yamamo2shun1/JUMBLEQ/STM32CubeIDE/JUMBLEQ/Appli/Core/Inc/led_control.h

/*
 * led_control.h
 *
 *  Created on: Nov 13, 2025
 *      Author: Shunichi Yamamoto
 */

#ifndef INC_LED_CONTROL_H_
#define INC_LED_CONTROL_H_

#include <stdint.h>

void led_update_color_state(void);
void led_reset_buffer(void);

void led_tx_blinking_task(void);
void led_rx_blinking_task(void);

void led_set_color(uint8_t index, uint8_t red, uint8_t green, uint8_t blue);
void led_renew_buffer(void);
void led_rgb_task(void);
void led_notify_save_success(void);

#endif /* INC_LED_CONTROL_H_ */
