yamamo2shun1/JUMBLEQ/STM32CubeIDE/JUMBLEQ/Appli/Core/Inc/JUMBLEQ_DSP_ADAU146xSchematic_1.h

/* 
 * File:	C:\Users\shun\JUMBLEQ\SigmaStudio+\exported_code\JUMBLEQ_DSP_ADAU146xSchematic_1.h
 * Created:	Tuesday, 15 September 2026 12:42 PM
 * Description:	ADAU146xSchematic_1 program data.
 * 
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
 * This software may only be used to program products purchased from 
 * Analog Devices for incorporation by you into audio products that 
 * are intended for resale to audio product end users.This software 
 * may not be distributed whole or in any part to third parties. 
 * 
 * Copyright © 2026 Analog Devices, Inc. All rights reserved.
 */

#include "SigmaStudioFW.h"

#ifndef __JUMBLEQ_DSP_ADAU146XSCHEMATIC_1_H__
#define __JUMBLEQ_DSP_ADAU146XSCHEMATIC_1_H__

/* DSP Ram Data */
#define DM1_DATA_SIZE_ADAU146XSCHEMATIC_1 912
#define DM1_DATA_ADDR_ADAU146XSCHEMATIC_1 24576
ADI_REG_TYPE DM1_DATA_ADAU146XSCHEMATIC_1_Data[DM1_DATA_SIZE_ADAU146XSCHEMATIC_1] = {
0x00, 0x00, 0x00, 0x00, 
0x00, 0x00, 0x00, 0x00, 
0x00, 0x00, 0x00, 0x00, 
0x00, 0x00, 0x00, 0x00, 
0x00, 0x00, 0x00, 0x00, 
0x00, 0x00, 0x00, 0x00, 
0x00, 0x00, 0x00, 0x00, 
0x00, 0x00, 0x00, 0x00, 
0x00, 0x00, 0x00, 0x00, 
0x00, 0x00, 0x20, 0x8A, 
0x00, 0x00, 0x00, 0x00, 
0x00, 0x00, 0x04, 0x10, 
0x00, 0x00, 0x00, 0x00, 
0x00, 0x00, 0x20, 0x8A, 
0x00, 0x00, 0x00, 0x00, 
0x00, 0x00, 0x04, 0x10, 
0x00, 0x00, 0x00, 0x00, 
0x00, 0x00, 0x20, 0x8A, 
0x00, 0x00, 0x00, 0x00, 
0x00, 0x00, 0x00, 0x00, 
0x00, 0x00, 0x00, 0x00, 
0x00, 0x00, 0x00, 0x00, 
0x00, 0x00, 0x00, 0x00, 
0x00, 0x00, 0x00, 0x00, 
0x00, 0x00, 0x00, 0x00, 
0x00, 0x00, 0x00, 0x00, 
0x00, 0x00, 0x00, 0x00, 
0x00, 0x00, 0x00, 0x00, 
0x00, 0x00, 0x00, 0x00, 
0x00, 0x00, 0x00, 0x00, 
0x00, 0x00, 0x00, 0x00, 
0x00, 0x00, 0x00, 0x00, 
0x00, 0x00, 0x00, 0x00, 
0x00, 0x00, 0x00, 0x00, 
0x00, 0x00, 0x00, 0x00, 
0x00, 0x00, 0x00, 0x00, 
0x00, 0x00, 0x00, 0x00, 
0x00, 0x00, 0x00, 0x00, 
0x00, 0x00, 0x00, 0x00, 
0x00, 0x00, 0x00, 0x00, 
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
};

/* DSP Program Data */
#define PROGRAM_DATA_SIZE_ADAU146XSCHEMATIC_1 2936
#define PROGRAM_DATA_ADDR_ADAU146XSCHEMATIC_1 49152
ADI_REG_TYPE PROGRAM_DATA_ADAU146XSCHEMATIC_1_Data[PROGRAM_DATA_SIZE_ADAU146XSCHEMATIC_1] = {
0x00, 0x00, 0x00, 0x02, 
0x0C, 0x00, 0xDC, 0xDC, 
0x0D, 0x00, 0xFF, 0xD2, 
0x0D, 0x00, 0xFF, 0xD0, 
0x0D, 0x00, 0xF4, 0x50, 
0x0D, 0x00, 0xF4, 0x00, 
0xC0, 0x00, 0x23, 0x80, 
0x80, 0x00, 0x00, 0x00, 
0xC0, 0x00, 0x23, 0x00, 
0x80, 0x00, 0x00, 0x00, 
0xC0, 0x00, 0x23, 0xC0, 
0x80, 0x00, 0x00, 0x10, 
0xC0, 0x00, 0x22, 0x00, 
0x80, 0x00, 0x00, 0x00, 
0x08, 0x80, 0xDC, 0xE0, 
0x0C, 0x00, 0xDC, 0xDC, 
0x0A, 0x21, 0x00, 0x12, 
0x08, 0x00, 0x00, 0x10, 
0x01, 0x00, 0x00, 0x14, 
0x06, 0x40, 0x40, 0x10, 
0x0A, 0x21, 0x00, 0x16, 
0x08, 0x00, 0x00, 0x14, 
0x01, 0x00, 0x00, 0x18, 
0x06, 0x40, 0x50, 0x10, 
0x0A, 0x21, 0x00, 0x1A, 
0x08, 0x00, 0x00, 0x18, 
0x01, 0x00, 0x00, 0x1C, 
0x06, 0x40, 0x50, 0x10, 
0xC0, 0x00, 0x20, 0x00, 
0x80, 0x00, 0x00, 0x2F, 
0x0D, 0x00, 0xFF, 0xC1, 
0xC0, 0x00, 0x20, 0x00, 
0x80, 0x00, 0x00, 0x01, 
0x0D, 0x00, 0xF4, 0x62, 
0xC0, 0x00, 0x20, 0x00, 
0x80, 0x00, 0x00, 0x00, 
0x0D, 0x00, 0xF4, 0x62, 
0xC0, 0x00, 0x20, 0x00, 
0x80, 0x00, 0x00, 0x02, 
0x0D, 0x00, 0xFF, 0xD1, 
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
};

/* DSP Parameter (Coefficient) Data */
#define DM0_DATA_SIZE_ADAU146XSCHEMATIC_1 696
#define DM0_DATA_ADDR_ADAU146XSCHEMATIC_1 0
ADI_REG_TYPE DM0_DATA_ADAU146XSCHEMATIC_1_Data[DM0_DATA_SIZE_ADAU146XSCHEMATIC_1] = {
0x00, 0x00, 0x00, 0x00, 
0x00, 0x00, 0x00, 0x00, 
0x00, 0x00, 0x00, 0x00, 
0x00, 0x00, 0x00, 0x00, 
0x00, 0x00, 0x00, 0x00, 
0x00, 0x00, 0x00, 0x00, 
0x00, 0x00, 0x00, 0x00, 
0x00, 0x00, 0x00, 0x00, 
0x00, 0x00, 0x00, 0x00, 
0x00, 0x00, 0x00, 0x00, 
0x00, 0x00, 0x00, 0x00, 
0x00, 0x00, 0x00, 0x00, 
0x00, 0x00, 0x00, 0x00, 
0x00, 0x00, 0x00, 0x00, 
0x00, 0x00, 0x00, 0x00, 
0x00, 0x00, 0x00, 0x00, 
0x00, 0x00, 0x00, 0x5C, 
0x00, 0x00, 0x00, 0x5C, 
0x00, 0x00, 0x00, 0x0C, 
0x00, 0x00, 0x00, 0x00, 
0x00, 0x00, 0x00, 0x14, 
0x00, 0x00, 0x00, 0x14, 
0x00, 0x00, 0x00, 0x90, 
0x00, 0x00, 0x00, 0x00, 
0x00, 0x00, 0x00, 0xA4, 
0x00, 0x00, 0x00, 0xA4, 
0x00, 0x00, 0x00, 0x3C, 
0x00, 0x00, 0x00, 0x00, 
0xFF, 0x00, 0x62, 0xF7, 
0x01, 0xFF, 0x3A, 0x12, 
0xFF, 0x00, 0x62, 0xF7, 
0xFF, 0x00, 0xC5, 0xD7, 
0x01, 0xFF, 0x39, 0xFC, 
0xFF, 0x00, 0x29, 0x0E, 
0x01, 0xFF, 0xAD, 0xE4, 
0xFF, 0x00, 0x29, 0x0E, 
0xFF, 0x00, 0x52, 0x05, 
0x01, 0xFF, 0xAD, 0xCE, 
0xFF, 0xEF, 0xD6, 0xFE, 
0x00, 0x00, 0x89, 0xC6, 
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
};

/* Register Default - SOFT_RESET */
#define R0_SOFT_RESET_SIZE_ADAU146XSCHEMATIC_1 2
#define R0_SOFT_RESET_ADDR_ADAU146XSCHEMATIC_1 63632
ADI_REG_TYPE R0_SOFT_RESET_ADAU146XSCHEMATIC_1_Data[R0_SOFT_RESET_SIZE_ADAU146XSCHEMATIC_1] = {
0x00, 0x00, 
};

/* Register Default - SOFT_RESET */
#define R1_SOFT_RESET_SIZE_ADAU146XSCHEMATIC_1 2
#define R1_SOFT_RESET_ADDR_ADAU146XSCHEMATIC_1 63632
ADI_REG_TYPE R1_SOFT_RESET_ADAU146XSCHEMATIC_1_Data[R1_SOFT_RESET_SIZE_ADAU146XSCHEMATIC_1] = {
0x00, 0x01, 
};

/* Register Default - Reset Delay */
#define R2_RESET_DELAY_SIZE_ADAU146XSCHEMATIC_1 2
#define R2_RESET_DELAY_ADDR_ADAU146XSCHEMATIC_1 0
ADI_REG_TYPE R2_RESET_DELAY_ADAU146XSCHEMATIC_1_Data[R2_RESET_DELAY_SIZE_ADAU146XSCHEMATIC_1] = {
0x00, 0xFF, 
};

/* Register Default - HIBERNATE */
#define R3_HIBERNATE_SIZE_ADAU146XSCHEMATIC_1 2
#define R3_HIBERNATE_ADDR_ADAU146XSCHEMATIC_1 62464
ADI_REG_TYPE R3_HIBERNATE_ADAU146XSCHEMATIC_1_Data[R3_HIBERNATE_SIZE_ADAU146XSCHEMATIC_1] = {
0x00, 0x00, 
};

/* Register Default - HIBERNATE */
#define R4_HIBERNATE_SIZE_ADAU146XSCHEMATIC_1 2
#define R4_HIBERNATE_ADDR_ADAU146XSCHEMATIC_1 62464
ADI_REG_TYPE R4_HIBERNATE_ADAU146XSCHEMATIC_1_Data[R4_HIBERNATE_SIZE_ADAU146XSCHEMATIC_1] = {
0x00, 0x01, 
};

/* Register Default - Hibernate Delay */
#define R5_HIBERNATE_DELAY_SIZE_ADAU146XSCHEMATIC_1 2
#define R5_HIBERNATE_DELAY_ADDR_ADAU146XSCHEMATIC_1 0
ADI_REG_TYPE R5_HIBERNATE_DELAY_ADAU146XSCHEMATIC_1_Data[R5_HIBERNATE_DELAY_SIZE_ADAU146XSCHEMATIC_1] = {
0x00, 0xFF, 
};

/* Register Default - KILL_CORE */
#define R6_KILL_CORE_SIZE_ADAU146XSCHEMATIC_1 2
#define R6_KILL_CORE_ADDR_ADAU146XSCHEMATIC_1 62467
ADI_REG_TYPE R6_KILL_CORE_ADAU146XSCHEMATIC_1_Data[R6_KILL_CORE_SIZE_ADAU146XSCHEMATIC_1] = {
0x00, 0x00, 
};

/* Register Default - KILL_CORE */
#define R7_KILL_CORE_SIZE_ADAU146XSCHEMATIC_1 2
#define R7_KILL_CORE_ADDR_ADAU146XSCHEMATIC_1 62467
ADI_REG_TYPE R7_KILL_CORE_ADAU146XSCHEMATIC_1_Data[R7_KILL_CORE_SIZE_ADAU146XSCHEMATIC_1] = {
0x00, 0x01, 
};

/* Register Default - PLL_ENABLE */
#define R8_PLL_ENABLE_SIZE_ADAU146XSCHEMATIC_1 2
#define R8_PLL_ENABLE_ADDR_ADAU146XSCHEMATIC_1 61443
ADI_REG_TYPE R8_PLL_ENABLE_ADAU146XSCHEMATIC_1_Data[R8_PLL_ENABLE_SIZE_ADAU146XSCHEMATIC_1] = {
0x00, 0x00, 
};

/* Register Default - PLL_CTRL1 Register */
#define R9_PLL_CTRL1_REGISTER_SIZE_ADAU146XSCHEMATIC_1 2
#define R9_PLL_CTRL1_REGISTER_ADDR_ADAU146XSCHEMATIC_1 61441
ADI_REG_TYPE R9_PLL_CTRL1_REGISTER_ADAU146XSCHEMATIC_1_Data[R9_PLL_CTRL1_REGISTER_SIZE_ADAU146XSCHEMATIC_1] = {
0x00, 0x02, 
};

/* Register Default - PLL_CLK_SRC Register */
#define R10_PLL_CLK_SRC_REGISTER_SIZE_ADAU146XSCHEMATIC_1 2
#define R10_PLL_CLK_SRC_REGISTER_ADDR_ADAU146XSCHEMATIC_1 61442
ADI_REG_TYPE R10_PLL_CLK_SRC_REGISTER_ADAU146XSCHEMATIC_1_Data[R10_PLL_CLK_SRC_REGISTER_SIZE_ADAU146XSCHEMATIC_1] = {
0x00, 0x01, 
};

/* Register Default - MCLK_OUT Register */
#define R11_MCLK_OUT_REGISTER_SIZE_ADAU146XSCHEMATIC_1 2
#define R11_MCLK_OUT_REGISTER_ADDR_ADAU146XSCHEMATIC_1 61445
ADI_REG_TYPE R11_MCLK_OUT_REGISTER_ADAU146XSCHEMATIC_1_Data[R11_MCLK_OUT_REGISTER_SIZE_ADAU146XSCHEMATIC_1] = {
0x00, 0x07, 
};

/* Register Default - PLL_ENABLE Register */
#define R12_PLL_ENABLE_REGISTER_SIZE_ADAU146XSCHEMATIC_1 2
#define R12_PLL_ENABLE_REGISTER_ADDR_ADAU146XSCHEMATIC_1 61443
ADI_REG_TYPE R12_PLL_ENABLE_REGISTER_ADAU146XSCHEMATIC_1_Data[R12_PLL_ENABLE_REGISTER_SIZE_ADAU146XSCHEMATIC_1] = {
0x00, 0x01, 
};

/* Register Default - PLL Lock Delay */
#define R13_PLL_LOCK_DELAY_SIZE_ADAU146XSCHEMATIC_1 2
#define R13_PLL_LOCK_DELAY_ADDR_ADAU146XSCHEMATIC_1 0
ADI_REG_TYPE R13_PLL_LOCK_DELAY_ADAU146XSCHEMATIC_1_Data[R13_PLL_LOCK_DELAY_SIZE_ADAU146XSCHEMATIC_1] = {
0x00, 0xFF, 
};

/* Register Default - POWER_ENABLE0 Register */
#define R14_POWER_ENABLE0_REGISTER_SIZE_ADAU146XSCHEMATIC_1 2
#define R14_POWER_ENABLE0_REGISTER_ADDR_ADAU146XSCHEMATIC_1 61520
ADI_REG_TYPE R14_POWER_ENABLE0_REGISTER_ADAU146XSCHEMATIC_1_Data[R14_POWER_ENABLE0_REGISTER_SIZE_ADAU146XSCHEMATIC_1] = {
0x1F, 0xFF, 
};

/* Register Default - POWER_ENABLE1 Register */
#define R15_POWER_ENABLE1_REGISTER_SIZE_ADAU146XSCHEMATIC_1 2
#define R15_POWER_ENABLE1_REGISTER_ADDR_ADAU146XSCHEMATIC_1 61521
ADI_REG_TYPE R15_POWER_ENABLE1_REGISTER_ADAU146XSCHEMATIC_1_Data[R15_POWER_ENABLE1_REGISTER_SIZE_ADAU146XSCHEMATIC_1] = {
0x00, 0x1F, 
};

/* Register Default - CLK_GEN1_M */
#define R16_CLK_GEN1_M_SIZE_ADAU146XSCHEMATIC_1 2
#define R16_CLK_GEN1_M_ADDR_ADAU146XSCHEMATIC_1 61472
ADI_REG_TYPE R16_CLK_GEN1_M_ADAU146XSCHEMATIC_1_Data[R16_CLK_GEN1_M_SIZE_ADAU146XSCHEMATIC_1] = {
0x00, 0x03, 
};

/* Register Default - CLK_GEN2_M */
#define R17_CLK_GEN2_M_SIZE_ADAU146XSCHEMATIC_1 2
#define R17_CLK_GEN2_M_ADDR_ADAU146XSCHEMATIC_1 61474
ADI_REG_TYPE R17_CLK_GEN2_M_ADAU146XSCHEMATIC_1_Data[R17_CLK_GEN2_M_SIZE_ADAU146XSCHEMATIC_1] = {
0x00, 0x06, 
};

/* Register Default - ASRC_INPUT0 */
#define R18_ASRC_INPUT0_SIZE_ADAU146XSCHEMATIC_1 2
#define R18_ASRC_INPUT0_ADDR_ADAU146XSCHEMATIC_1 61696
ADI_REG_TYPE R18_ASRC_INPUT0_ADAU146XSCHEMATIC_1_Data[R18_ASRC_INPUT0_SIZE_ADAU146XSCHEMATIC_1] = {
0x00, 0x01, 
};

/* Register Default - ASRC_INPUT1 */
#define R19_ASRC_INPUT1_SIZE_ADAU146XSCHEMATIC_1 2
#define R19_ASRC_INPUT1_ADDR_ADAU146XSCHEMATIC_1 61697
ADI_REG_TYPE R19_ASRC_INPUT1_ADAU146XSCHEMATIC_1_Data[R19_ASRC_INPUT1_SIZE_ADAU146XSCHEMATIC_1] = {
0x00, 0x09, 
};

/* Register Default - ASRC_INPUT2 */
#define R20_ASRC_INPUT2_SIZE_ADAU146XSCHEMATIC_1 2
#define R20_ASRC_INPUT2_ADDR_ADAU146XSCHEMATIC_1 61698
ADI_REG_TYPE R20_ASRC_INPUT2_ADAU146XSCHEMATIC_1_Data[R20_ASRC_INPUT2_SIZE_ADAU146XSCHEMATIC_1] = {
0x00, 0x02, 
};

/* Register Default - ASRC_INPUT3 */
#define R21_ASRC_INPUT3_SIZE_ADAU146XSCHEMATIC_1 2
#define R21_ASRC_INPUT3_ADDR_ADAU146XSCHEMATIC_1 61699
ADI_REG_TYPE R21_ASRC_INPUT3_ADAU146XSCHEMATIC_1_Data[R21_ASRC_INPUT3_SIZE_ADAU146XSCHEMATIC_1] = {
0x00, 0x02, 
};

/* Register Default - ASRC_OUT_RATE0 */
#define R22_ASRC_OUT_RATE0_SIZE_ADAU146XSCHEMATIC_1 2
#define R22_ASRC_OUT_RATE0_ADDR_ADAU146XSCHEMATIC_1 61760
ADI_REG_TYPE R22_ASRC_OUT_RATE0_ADAU146XSCHEMATIC_1_Data[R22_ASRC_OUT_RATE0_SIZE_ADAU146XSCHEMATIC_1] = {
0x00, 0x05, 
};

/* Register Default - ASRC_OUT_RATE1 */
#define R23_ASRC_OUT_RATE1_SIZE_ADAU146XSCHEMATIC_1 2
#define R23_ASRC_OUT_RATE1_ADDR_ADAU146XSCHEMATIC_1 61761
ADI_REG_TYPE R23_ASRC_OUT_RATE1_ADAU146XSCHEMATIC_1_Data[R23_ASRC_OUT_RATE1_SIZE_ADAU146XSCHEMATIC_1] = {
0x00, 0x05, 
};

/* Register Default - ASRC_OUT_RATE2 */
#define R24_ASRC_OUT_RATE2_SIZE_ADAU146XSCHEMATIC_1 2
#define R24_ASRC_OUT_RATE2_ADDR_ADAU146XSCHEMATIC_1 61762
ADI_REG_TYPE R24_ASRC_OUT_RATE2_ADAU146XSCHEMATIC_1_Data[R24_ASRC_OUT_RATE2_SIZE_ADAU146XSCHEMATIC_1] = {
0x00, 0x01, 
};

/* Register Default - ASRC_OUT_RATE3 */
#define R25_ASRC_OUT_RATE3_SIZE_ADAU146XSCHEMATIC_1 2
#define R25_ASRC_OUT_RATE3_ADDR_ADAU146XSCHEMATIC_1 61763
ADI_REG_TYPE R25_ASRC_OUT_RATE3_ADAU146XSCHEMATIC_1_Data[R25_ASRC_OUT_RATE3_SIZE_ADAU146XSCHEMATIC_1] = {
0x00, 0x01, 
};

/* Register Default - SOUT_SOURCE0 */
#define R26_SOUT_SOURCE0_SIZE_ADAU146XSCHEMATIC_1 2
#define R26_SOUT_SOURCE0_ADDR_ADAU146XSCHEMATIC_1 61824
ADI_REG_TYPE R26_SOUT_SOURCE0_ADAU146XSCHEMATIC_1_Data[R26_SOUT_SOURCE0_SIZE_ADAU146XSCHEMATIC_1] = {
0x00, 0x13, 
};

/* Register Default - SOUT_SOURCE1 */
#define R27_SOUT_SOURCE1_SIZE_ADAU146XSCHEMATIC_1 2
#define R27_SOUT_SOURCE1_ADDR_ADAU146XSCHEMATIC_1 61825
ADI_REG_TYPE R27_SOUT_SOURCE1_ADAU146XSCHEMATIC_1_Data[R27_SOUT_SOURCE1_SIZE_ADAU146XSCHEMATIC_1] = {
0x00, 0x1B, 
};

/* Register Default - SOUT_SOURCE2 */
#define R28_SOUT_SOURCE2_SIZE_ADAU146XSCHEMATIC_1 2
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
0x90, 0x41, 
};

/* Register Default - SERIAL_BYTE_3_0 */
#define R54_SERIAL_BYTE_3_0_SIZE_ADAU146XSCHEMATIC_1 2
#define R54_SERIAL_BYTE_3_0_ADDR_ADAU146XSCHEMATIC_1 61964
ADI_REG_TYPE R54_SERIAL_BYTE_3_0_ADAU146XSCHEMATIC_1_Data[R54_SERIAL_BYTE_3_0_SIZE_ADAU146XSCHEMATIC_1] = {
0x90, 0x00, 
};

/* Register Default - SERIAL_BYTE_4_0 */
#define R55_SERIAL_BYTE_4_0_SIZE_ADAU146XSCHEMATIC_1 2
#define R55_SERIAL_BYTE_4_0_ADDR_ADAU146XSCHEMATIC_1 61968
ADI_REG_TYPE R55_SERIAL_BYTE_4_0_ADAU146XSCHEMATIC_1_Data[R55_SERIAL_BYTE_4_0_SIZE_ADAU146XSCHEMATIC_1] = {
0x90, 0x49, 
};

/* Register Default - SERIAL_BYTE_4_1 */
#define R56_SERIAL_BYTE_4_1_SIZE_ADAU146XSCHEMATIC_1 2
#define R56_SERIAL_BYTE_4_1_ADDR_ADAU146XSCHEMATIC_1 61969
ADI_REG_TYPE R56_SERIAL_BYTE_4_1_ADAU146XSCHEMATIC_1_Data[R56_SERIAL_BYTE_4_1_SIZE_ADAU146XSCHEMATIC_1] = {
0x00, 0x0A, 
};

/* Register Default - SERIAL_BYTE_5_0 */
#define R57_SERIAL_BYTE_5_0_SIZE_ADAU146XSCHEMATIC_1 2
#define R57_SERIAL_BYTE_5_0_ADDR_ADAU146XSCHEMATIC_1 61972
ADI_REG_TYPE R57_SERIAL_BYTE_5_0_ADAU146XSCHEMATIC_1_Data[R57_SERIAL_BYTE_5_0_SIZE_ADAU146XSCHEMATIC_1] = {
0x90, 0x41, 
};

/* Register Default - SERIAL_BYTE_6_0 */
#define R58_SERIAL_BYTE_6_0_SIZE_ADAU146XSCHEMATIC_1 2
#define R58_SERIAL_BYTE_6_0_ADDR_ADAU146XSCHEMATIC_1 61976
ADI_REG_TYPE R58_SERIAL_BYTE_6_0_ADAU146XSCHEMATIC_1_Data[R58_SERIAL_BYTE_6_0_SIZE_ADAU146XSCHEMATIC_1] = {
0x90, 0x40, 
};

/* Register Default - SERIAL_BYTE_7_0 */
#define R59_SERIAL_BYTE_7_0_SIZE_ADAU146XSCHEMATIC_1 2
#define R59_SERIAL_BYTE_7_0_ADDR_ADAU146XSCHEMATIC_1 61980
ADI_REG_TYPE R59_SERIAL_BYTE_7_0_ADAU146XSCHEMATIC_1_Data[R59_SERIAL_BYTE_7_0_SIZE_ADAU146XSCHEMATIC_1] = {
0x90, 0x00, 
};

/* Register Default - KILL_CORE */
#define R63_KILL_CORE_SIZE_ADAU146XSCHEMATIC_1 2
#define R63_KILL_CORE_ADDR_ADAU146XSCHEMATIC_1 62467
ADI_REG_TYPE R63_KILL_CORE_ADAU146XSCHEMATIC_1_Data[R63_KILL_CORE_SIZE_ADAU146XSCHEMATIC_1] = {
0x00, 0x00, 
};

/* Register Default - START_ADDRESS */
#define R64_START_ADDRESS_SIZE_ADAU146XSCHEMATIC_1 2
#define R64_START_ADDRESS_ADDR_ADAU146XSCHEMATIC_1 62468
ADI_REG_TYPE R64_START_ADDRESS_ADAU146XSCHEMATIC_1_Data[R64_START_ADDRESS_SIZE_ADAU146XSCHEMATIC_1] = {
0x00, 0x00, 
};

/* Register Default - START_PULSE */
#define R65_START_PULSE_SIZE_ADAU146XSCHEMATIC_1 2
#define R65_START_PULSE_ADDR_ADAU146XSCHEMATIC_1 62465
ADI_REG_TYPE R65_START_PULSE_ADAU146XSCHEMATIC_1_Data[R65_START_PULSE_SIZE_ADAU146XSCHEMATIC_1] = {
0x00, 0x02, 
};

/* Register Default - START_CORE */
#define R66_START_CORE_SIZE_ADAU146XSCHEMATIC_1 2
#define R66_START_CORE_ADDR_ADAU146XSCHEMATIC_1 62466
ADI_REG_TYPE R66_START_CORE_ADAU146XSCHEMATIC_1_Data[R66_START_CORE_SIZE_ADAU146XSCHEMATIC_1] = {
0x00, 0x00, 
};

/* Register Default - START_CORE */
#define R67_START_CORE_SIZE_ADAU146XSCHEMATIC_1 2
#define R67_START_CORE_ADDR_ADAU146XSCHEMATIC_1 62466
ADI_REG_TYPE R67_START_CORE_ADAU146XSCHEMATIC_1_Data[R67_START_CORE_SIZE_ADAU146XSCHEMATIC_1] = {
0x00, 0x01, 
};

/* Register Default - Start Delay */
#define R68_START_DELAY_SIZE_ADAU146XSCHEMATIC_1 2
#define R68_START_DELAY_ADDR_ADAU146XSCHEMATIC_1 0
ADI_REG_TYPE R68_START_DELAY_ADAU146XSCHEMATIC_1_Data[R68_START_DELAY_SIZE_ADAU146XSCHEMATIC_1] = {
0x00, 0x01, 
};

/* Register Default - HIBERNATE */
#define R69_HIBERNATE_SIZE_ADAU146XSCHEMATIC_1 2
#define R69_HIBERNATE_ADDR_ADAU146XSCHEMATIC_1 62464
ADI_REG_TYPE R69_HIBERNATE_ADAU146XSCHEMATIC_1_Data[R69_HIBERNATE_SIZE_ADAU146XSCHEMATIC_1] = {
0x00, 0x00, 
};

/* Default Download */
#define DEFAULT_DOWNLOAD_SIZE_ADAU146XSCHEMATIC_1 70

void default_download_ADAU146XSCHEMATIC_1()
{
	SIGMA_WRITE_REGISTER_BLOCK(DEVICE_ADDR_ADAU146XSCHEMATIC_1, R0_SOFT_RESET_ADDR_ADAU146XSCHEMATIC_1 , R0_SOFT_RESET_SIZE_ADAU146XSCHEMATIC_1 , R0_SOFT_RESET_ADAU146XSCHEMATIC_1_Data);
	SIGMA_WRITE_REGISTER_BLOCK(DEVICE_ADDR_ADAU146XSCHEMATIC_1, R1_SOFT_RESET_ADDR_ADAU146XSCHEMATIC_1 , R1_SOFT_RESET_SIZE_ADAU146XSCHEMATIC_1 , R1_SOFT_RESET_ADAU146XSCHEMATIC_1_Data);
	SIGMA_WRITE_DELAY(DEVICE_ADDR_ADAU146XSCHEMATIC_1, R2_RESET_DELAY_ADDR_ADAU146XSCHEMATIC_1 , R2_RESET_DELAY_SIZE_ADAU146XSCHEMATIC_1 , R2_RESET_DELAY_ADAU146XSCHEMATIC_1_Data);
	SIGMA_WRITE_REGISTER_BLOCK(DEVICE_ADDR_ADAU146XSCHEMATIC_1, R3_HIBERNATE_ADDR_ADAU146XSCHEMATIC_1 , R3_HIBERNATE_SIZE_ADAU146XSCHEMATIC_1 , R3_HIBERNATE_ADAU146XSCHEMATIC_1_Data);
	SIGMA_WRITE_REGISTER_BLOCK(DEVICE_ADDR_ADAU146XSCHEMATIC_1, R4_HIBERNATE_ADDR_ADAU146XSCHEMATIC_1 , R4_HIBERNATE_SIZE_ADAU146XSCHEMATIC_1 , R4_HIBERNATE_ADAU146XSCHEMATIC_1_Data);
	SIGMA_WRITE_DELAY(DEVICE_ADDR_ADAU146XSCHEMATIC_1, R5_HIBERNATE_DELAY_ADDR_ADAU146XSCHEMATIC_1 , R5_HIBERNATE_DELAY_SIZE_ADAU146XSCHEMATIC_1 , R5_HIBERNATE_DELAY_ADAU146XSCHEMATIC_1_Data);
	SIGMA_WRITE_REGISTER_BLOCK(DEVICE_ADDR_ADAU146XSCHEMATIC_1, R6_KILL_CORE_ADDR_ADAU146XSCHEMATIC_1 , R6_KILL_CORE_SIZE_ADAU146XSCHEMATIC_1 , R6_KILL_CORE_ADAU146XSCHEMATIC_1_Data);
	SIGMA_WRITE_REGISTER_BLOCK(DEVICE_ADDR_ADAU146XSCHEMATIC_1, R7_KILL_CORE_ADDR_ADAU146XSCHEMATIC_1 , R7_KILL_CORE_SIZE_ADAU146XSCHEMATIC_1 , R7_KILL_CORE_ADAU146XSCHEMATIC_1_Data);
	SIGMA_WRITE_REGISTER_BLOCK(DEVICE_ADDR_ADAU146XSCHEMATIC_1, R8_PLL_ENABLE_ADDR_ADAU146XSCHEMATIC_1 , R8_PLL_ENABLE_SIZE_ADAU146XSCHEMATIC_1 , R8_PLL_ENABLE_ADAU146XSCHEMATIC_1_Data);
	SIGMA_WRITE_REGISTER_BLOCK(DEVICE_ADDR_ADAU146XSCHEMATIC_1, R9_PLL_CTRL1_REGISTER_ADDR_ADAU146XSCHEMATIC_1 , R9_PLL_CTRL1_REGISTER_SIZE_ADAU146XSCHEMATIC_1 , R9_PLL_CTRL1_REGISTER_ADAU146XSCHEMATIC_1_Data);
	SIGMA_WRITE_REGISTER_BLOCK(DEVICE_ADDR_ADAU146XSCHEMATIC_1, R10_PLL_CLK_SRC_REGISTER_ADDR_ADAU146XSCHEMATIC_1 , R10_PLL_CLK_SRC_REGISTER_SIZE_ADAU146XSCHEMATIC_1 , R10_PLL_CLK_SRC_REGISTER_ADAU146XSCHEMATIC_1_Data);
	SIGMA_WRITE_REGISTER_BLOCK(DEVICE_ADDR_ADAU146XSCHEMATIC_1, R11_MCLK_OUT_REGISTER_ADDR_ADAU146XSCHEMATIC_1 , R11_MCLK_OUT_REGISTER_SIZE_ADAU146XSCHEMATIC_1 , R11_MCLK_OUT_REGISTER_ADAU146XSCHEMATIC_1_Data);
	SIGMA_WRITE_REGISTER_BLOCK(DEVICE_ADDR_ADAU146XSCHEMATIC_1, R12_PLL_ENABLE_REGISTER_ADDR_ADAU146XSCHEMATIC_1 , R12_PLL_ENABLE_REGISTER_SIZE_ADAU146XSCHEMATIC_1 , R12_PLL_ENABLE_REGISTER_ADAU146XSCHEMATIC_1_Data);
	SIGMA_WRITE_DELAY(DEVICE_ADDR_ADAU146XSCHEMATIC_1, R13_PLL_LOCK_DELAY_ADDR_ADAU146XSCHEMATIC_1 , R13_PLL_LOCK_DELAY_SIZE_ADAU146XSCHEMATIC_1 , R13_PLL_LOCK_DELAY_ADAU146XSCHEMATIC_1_Data);
	SIGMA_WRITE_REGISTER_BLOCK(DEVICE_ADDR_ADAU146XSCHEMATIC_1, R14_POWER_ENABLE0_REGISTER_ADDR_ADAU146XSCHEMATIC_1 , R14_POWER_ENABLE0_REGISTER_SIZE_ADAU146XSCHEMATIC_1 , R14_POWER_ENABLE0_REGISTER_ADAU146XSCHEMATIC_1_Data);
	SIGMA_WRITE_REGISTER_BLOCK(DEVICE_ADDR_ADAU146XSCHEMATIC_1, R15_POWER_ENABLE1_REGISTER_ADDR_ADAU146XSCHEMATIC_1 , R15_POWER_ENABLE1_REGISTER_SIZE_ADAU146XSCHEMATIC_1 , R15_POWER_ENABLE1_REGISTER_ADAU146XSCHEMATIC_1_Data);
	SIGMA_WRITE_REGISTER_BLOCK(DEVICE_ADDR_ADAU146XSCHEMATIC_1, R16_CLK_GEN1_M_ADDR_ADAU146XSCHEMATIC_1 , R16_CLK_GEN1_M_SIZE_ADAU146XSCHEMATIC_1 , R16_CLK_GEN1_M_ADAU146XSCHEMATIC_1_Data);
	SIGMA_WRITE_REGISTER_BLOCK(DEVICE_ADDR_ADAU146XSCHEMATIC_1, R17_CLK_GEN2_M_ADDR_ADAU146XSCHEMATIC_1 , R17_CLK_GEN2_M_SIZE_ADAU146XSCHEMATIC_1 , R17_CLK_GEN2_M_ADAU146XSCHEMATIC_1_Data);
	SIGMA_WRITE_REGISTER_BLOCK(DEVICE_ADDR_ADAU146XSCHEMATIC_1, R18_ASRC_INPUT0_ADDR_ADAU146XSCHEMATIC_1 , R18_ASRC_INPUT0_SIZE_ADAU146XSCHEMATIC_1 , R18_ASRC_INPUT0_ADAU146XSCHEMATIC_1_Data);
	SIGMA_WRITE_REGISTER_BLOCK(DEVICE_ADDR_ADAU146XSCHEMATIC_1, R19_ASRC_INPUT1_ADDR_ADAU146XSCHEMATIC_1 , R19_ASRC_INPUT1_SIZE_ADAU146XSCHEMATIC_1 , R19_ASRC_INPUT1_ADAU146XSCHEMATIC_1_Data);
	SIGMA_WRITE_REGISTER_BLOCK(DEVICE_ADDR_ADAU146XSCHEMATIC_1, R20_ASRC_INPUT2_ADDR_ADAU146XSCHEMATIC_1 , R20_ASRC_INPUT2_SIZE_ADAU146XSCHEMATIC_1 , R20_ASRC_INPUT2_ADAU146XSCHEMATIC_1_Data);
	SIGMA_WRITE_REGISTER_BLOCK(DEVICE_ADDR_ADAU146XSCHEMATIC_1, R21_ASRC_INPUT3_ADDR_ADAU146XSCHEMATIC_1 , R21_ASRC_INPUT3_SIZE_ADAU146XSCHEMATIC_1 , R21_ASRC_INPUT3_ADAU146XSCHEMATIC_1_Data);
	SIGMA_WRITE_REGISTER_BLOCK(DEVICE_ADDR_ADAU146XSCHEMATIC_1, R22_ASRC_OUT_RATE0_ADDR_ADAU146XSCHEMATIC_1 , R22_ASRC_OUT_RATE0_SIZE_ADAU146XSCHEMATIC_1 , R22_ASRC_OUT_RATE0_ADAU146XSCHEMATIC_1_Data);
	SIGMA_WRITE_REGISTER_BLOCK(DEVICE_ADDR_ADAU146XSCHEMATIC_1, R23_ASRC_OUT_RATE1_ADDR_ADAU146XSCHEMATIC_1 , R23_ASRC_OUT_RATE1_SIZE_ADAU146XSCHEMATIC_1 , R23_ASRC_OUT_RATE1_ADAU146XSCHEMATIC_1_Data);
	SIGMA_WRITE_REGISTER_BLOCK(DEVICE_ADDR_ADAU146XSCHEMATIC_1, R24_ASRC_OUT_RATE2_ADDR_ADAU146XSCHEMATIC_1 , R24_ASRC_OUT_RATE2_SIZE_ADAU146XSCHEMATIC_1 , R24_ASRC_OUT_RATE2_ADAU146XSCHEMATIC_1_Data);
	SIGMA_WRITE_REGISTER_BLOCK(DEVICE_ADDR_ADAU146XSCHEMATIC_1, R25_ASRC_OUT_RATE3_ADDR_ADAU146XSCHEMATIC_1 , R25_ASRC_OUT_RATE3_SIZE_ADAU146XSCHEMATIC_1 , R25_ASRC_OUT_RATE3_ADAU146XSCHEMATIC_1_Data);
	SIGMA_WRITE_REGISTER_BLOCK(DEVICE_ADDR_ADAU146XSCHEMATIC_1, R26_SOUT_SOURCE0_ADDR_ADAU146XSCHEMATIC_1 , R26_SOUT_SOURCE0_SIZE_ADAU146XSCHEMATIC_1 , R26_SOUT_SOURCE0_ADAU146XSCHEMATIC_1_Data);
	SIGMA_WRITE_REGISTER_BLOCK(DEVICE_ADDR_ADAU146XSCHEMATIC_1, R27_SOUT_SOURCE1_ADDR_ADAU146XSCHEMATIC_1 , R27_SOUT_SOURCE1_SIZE_ADAU146XSCHEMATIC_1 , R27_SOUT_SOURCE1_ADAU146XSCHEMATIC_1_Data);
	SIGMA_WRITE_REGISTER_BLOCK(DEVICE_ADDR_ADAU146XSCHEMATIC_1, R28_SOUT_SOURCE2_ADDR_ADAU146XSCHEMATIC_1 , R28_SOUT_SOURCE2_SIZE_ADAU146XSCHEMATIC_1 , R28_SOUT_SOURCE2_ADAU146XSCHEMATIC_1_Data);
	SIGMA_WRITE_REGISTER_BLOCK(DEVICE_ADDR_ADAU146XSCHEMATIC_1, R29_SOUT_SOURCE3_ADDR_ADAU146XSCHEMATIC_1 , R29_SOUT_SOURCE3_SIZE_ADAU146XSCHEMATIC_1 , R29_SOUT_SOURCE3_ADAU146XSCHEMATIC_1_Data);
	SIGMA_WRITE_REGISTER_BLOCK(DEVICE_ADDR_ADAU146XSCHEMATIC_1, R30_SOUT_SOURCE4_ADDR_ADAU146XSCHEMATIC_1 , R30_SOUT_SOURCE4_SIZE_ADAU146XSCHEMATIC_1 , R30_SOUT_SOURCE4_ADAU146XSCHEMATIC_1_Data);
	SIGMA_WRITE_REGISTER_BLOCK(DEVICE_ADDR_ADAU146XSCHEMATIC_1, R31_SOUT_SOURCE5_ADDR_ADAU146XSCHEMATIC_1 , R31_SOUT_SOURCE5_SIZE_ADAU146XSCHEMATIC_1 , R31_SOUT_SOURCE5_ADAU146XSCHEMATIC_1_Data);
	SIGMA_WRITE_REGISTER_BLOCK(DEVICE_ADDR_ADAU146XSCHEMATIC_1, R32_SOUT_SOURCE6_ADDR_ADAU146XSCHEMATIC_1 , R32_SOUT_SOURCE6_SIZE_ADAU146XSCHEMATIC_1 , R32_SOUT_SOURCE6_ADAU146XSCHEMATIC_1_Data);
	SIGMA_WRITE_REGISTER_BLOCK(DEVICE_ADDR_ADAU146XSCHEMATIC_1, R33_SOUT_SOURCE7_ADDR_ADAU146XSCHEMATIC_1 , R33_SOUT_SOURCE7_SIZE_ADAU146XSCHEMATIC_1 , R33_SOUT_SOURCE7_ADAU146XSCHEMATIC_1_Data);
	SIGMA_WRITE_REGISTER_BLOCK(DEVICE_ADDR_ADAU146XSCHEMATIC_1, R34_SOUT_SOURCE8_ADDR_ADAU146XSCHEMATIC_1 , R34_SOUT_SOURCE8_SIZE_ADAU146XSCHEMATIC_1 , R34_SOUT_SOURCE8_ADAU146XSCHEMATIC_1_Data);
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
	SIGMA_WRITE_REGISTER_BLOCK(DEVICE_ADDR_ADAU146XSCHEMATIC_1, R57_SERIAL_BYTE_5_0_ADDR_ADAU146XSCHEMATIC_1 , R57_SERIAL_BYTE_5_0_SIZE_ADAU146XSCHEMATIC_1 , R57_SERIAL_BYTE_5_0_ADAU146XSCHEMATIC_1_Data);
	SIGMA_WRITE_REGISTER_BLOCK(DEVICE_ADDR_ADAU146XSCHEMATIC_1, R58_SERIAL_BYTE_6_0_ADDR_ADAU146XSCHEMATIC_1 , R58_SERIAL_BYTE_6_0_SIZE_ADAU146XSCHEMATIC_1 , R58_SERIAL_BYTE_6_0_ADAU146XSCHEMATIC_1_Data);
	SIGMA_WRITE_REGISTER_BLOCK(DEVICE_ADDR_ADAU146XSCHEMATIC_1, R59_SERIAL_BYTE_7_0_ADDR_ADAU146XSCHEMATIC_1 , R59_SERIAL_BYTE_7_0_SIZE_ADAU146XSCHEMATIC_1 , R59_SERIAL_BYTE_7_0_ADAU146XSCHEMATIC_1_Data);
	SIGMA_WRITE_REGISTER_BLOCK(DEVICE_ADDR_ADAU146XSCHEMATIC_1, PROGRAM_DATA_ADDR_ADAU146XSCHEMATIC_1 , PROGRAM_DATA_SIZE_ADAU146XSCHEMATIC_1 , PROGRAM_DATA_ADAU146XSCHEMATIC_1_Data);
	SIGMA_WRITE_REGISTER_BLOCK(DEVICE_ADDR_ADAU146XSCHEMATIC_1, DM0_DATA_ADDR_ADAU146XSCHEMATIC_1 , DM0_DATA_SIZE_ADAU146XSCHEMATIC_1 , DM0_DATA_ADAU146XSCHEMATIC_1_Data);
	SIGMA_WRITE_REGISTER_BLOCK(DEVICE_ADDR_ADAU146XSCHEMATIC_1, DM1_DATA_ADDR_ADAU146XSCHEMATIC_1 , DM1_DATA_SIZE_ADAU146XSCHEMATIC_1 , DM1_DATA_ADAU146XSCHEMATIC_1_Data);
	SIGMA_WRITE_REGISTER_BLOCK(DEVICE_ADDR_ADAU146XSCHEMATIC_1, R63_KILL_CORE_ADDR_ADAU146XSCHEMATIC_1 , R63_KILL_CORE_SIZE_ADAU146XSCHEMATIC_1 , R63_KILL_CORE_ADAU146XSCHEMATIC_1_Data);
	SIGMA_WRITE_REGISTER_BLOCK(DEVICE_ADDR_ADAU146XSCHEMATIC_1, R64_START_ADDRESS_ADDR_ADAU146XSCHEMATIC_1 , R64_START_ADDRESS_SIZE_ADAU146XSCHEMATIC_1 , R64_START_ADDRESS_ADAU146XSCHEMATIC_1_Data);
	SIGMA_WRITE_REGISTER_BLOCK(DEVICE_ADDR_ADAU146XSCHEMATIC_1, R65_START_PULSE_ADDR_ADAU146XSCHEMATIC_1 , R65_START_PULSE_SIZE_ADAU146XSCHEMATIC_1 , R65_START_PULSE_ADAU146XSCHEMATIC_1_Data);
	SIGMA_WRITE_REGISTER_BLOCK(DEVICE_ADDR_ADAU146XSCHEMATIC_1, R66_START_CORE_ADDR_ADAU146XSCHEMATIC_1 , R66_START_CORE_SIZE_ADAU146XSCHEMATIC_1 , R66_START_CORE_ADAU146XSCHEMATIC_1_Data);
	SIGMA_WRITE_REGISTER_BLOCK(DEVICE_ADDR_ADAU146XSCHEMATIC_1, R67_START_CORE_ADDR_ADAU146XSCHEMATIC_1 , R67_START_CORE_SIZE_ADAU146XSCHEMATIC_1 , R67_START_CORE_ADAU146XSCHEMATIC_1_Data);
	SIGMA_WRITE_DELAY(DEVICE_ADDR_ADAU146XSCHEMATIC_1, R68_START_DELAY_ADDR_ADAU146XSCHEMATIC_1 , R68_START_DELAY_SIZE_ADAU146XSCHEMATIC_1 , R68_START_DELAY_ADAU146XSCHEMATIC_1_Data);
	SIGMA_WRITE_REGISTER_BLOCK(DEVICE_ADDR_ADAU146XSCHEMATIC_1, R69_HIBERNATE_ADDR_ADAU146XSCHEMATIC_1 , R69_HIBERNATE_SIZE_ADAU146XSCHEMATIC_1 , R69_HIBERNATE_ADAU146XSCHEMATIC_1_Data);
}
#endif
