yamamo2shun1/JUMBLEQ/STM32CubeIDE/JUMBLEQ/Appli/Core/Src/adau1466.c

/*
 * adau1466.c
 *
 *  Created on: 2026/01/24
 *      Author: Shunichi Yamamoto
 */

#include "adau1466.h"

#include <math.h>

#include "main.h"

#include "SigmaStudioFW.h"
#include "sigma_spi.h"
#include "JUMBLEQ_DSP_ADAU146xSchematic_1.h"
#include "JUMBLEQ_DSP_ADAU146xSchematic_1_Defines.h"
#include "JUMBLEQ_DSP_ADAU146xSchematic_1_PARAM.h"

#include "cmsis_os2.h"

_Static_assert((PROGRAM_DATA_SIZE_ADAU146XSCHEMATIC_1 % 4U) == 0U,
               "SigmaStudio program data must contain complete 32-bit words");
_Static_assert((DM0_DATA_SIZE_ADAU146XSCHEMATIC_1 % 4U) == 0U,
               "SigmaStudio DM0 data must contain complete 32-bit words");
_Static_assert((DM1_DATA_SIZE_ADAU146XSCHEMATIC_1 % 4U) == 0U,
               "SigmaStudio DM1 data must contain complete 32-bit words");

#define ADAU1466_REG_PLL_LOCK     0xF004U
#define ADAU1466_REG_CLK_GEN2_M   0xF022U
#define ADAU1466_REG_SOUT_SOURCE0 0xF180U

#define ADAU1466_PLL_LOCK_TIMEOUT_MS 200U
#define ADAU1466_CLOCK_SETTLE_MS     2U
#define ADAU1466_CORE_SAMPLE_RATE_HZ 96000U

#define ADAU1466_USB_MUX_DIRECT 0U
#define ADAU1466_USB_MUX_ASRC   4U

#define ADAU1466_SOUT_FROM_DSP   0x02U
#define ADAU1466_SOUT0_FROM_ASRC2 0x13U
#define ADAU1466_SOUT1_FROM_ASRC3 0x1BU

typedef struct
{
    uint32_t hz;
    uint8_t clk_gen2_m;
    uint8_t sout_source0;
    uint8_t sout_source1;
    uint32_t usb_mux_index;
} adau1466_sample_rate_cfg_t;

typedef struct
{
    uint8_t channel;
    uint16_t addr;
} adau1466_channel_addr_t;

typedef struct
{
    uint8_t channel;
    uint16_t addr;
    uint8_t mem_page;
} adau1466_safeload_selector_t;

// USB channels are 1-based in the UAC API.
enum
{
    ADAU1466_USB_CH_COUNT = 4U,
};

static const uint16_t s_usb_gain_addr[ADAU1466_USB_CH_COUNT] = {
    MOD_INPUT_FROM_USB1_GAIN_ADDR,
    MOD_INPUT_FROM_USB2_GAIN_ADDR,
    MOD_INPUT_FROM_USB3_GAIN_ADDR,
    MOD_INPUT_FROM_USB4_GAIN_ADDR,
};

static const uint16_t s_usb_mute_addr[ADAU1466_USB_CH_COUNT] = {
    MOD_MUTE_USB1_MUTE_ADDR,
    MOD_MUTE_USB2_MUTE_ADDR,
    MOD_MUTE_USB3_MUTE_ADDR,
    MOD_MUTE_USB4_MUTE_ADDR,
};

enum
{
    ADAU1466_DC_INPUT_A = 0,
    ADAU1466_DC_INPUT_B,
    ADAU1466_DC_INPUT_COUNT,
};

static const uint16_t s_dc_input_addr[ADAU1466_DC_INPUT_COUNT] = {
    MOD_DCINPUT_A_DCVALUE_ADDR,
    MOD_DCINPUT_B_DCVALUE_ADDR,
};

enum
{
    ADAU1466_DRY_DC_A = 0,
    ADAU1466_DRY_DC_B,
    ADAU1466_DRY_DC_COUNT,
};

static const uint16_t s_dry_dc_addr[ADAU1466_DRY_DC_COUNT] = {
    MOD_DCINPUT_DRYA_DCVALUE_ADDR,
    MOD_DCINPUT_DRYB_DCVALUE_ADDR,
};

enum
{
    ADAU1466_CH_FADER_TARGET_A = 0,
    ADAU1466_CH_FADER_TARGET_B,
    ADAU1466_CH_FADER_TARGET_POST,
    ADAU1466_CH_FADER_TARGET_COUNT,
};

static const uint16_t s_ch_fader_assign_addr[ADAU1466_CH_FADER_TARGET_COUNT] = {
    MOD_CH_FADER_ASSIGN_SW_A_INDEX_ADDR,
    MOD_CH_FADER_ASSIGN_SW_B_INDEX_ADDR,
    MOD_CH_FADER_ASSIGN_SW_POST_INDEX_ADDR,
};

static const adau1466_channel_addr_t s_send_source_addr[] = {
    {AUDIO_INPUT_SOURCE_CH1, MOD_SEND_SW_1_INDEX_ADDR},
    {AUDIO_INPUT_SOURCE_CH2, MOD_SEND_SW_2_INDEX_ADDR},
};

static const adau1466_safeload_selector_t s_input_type_selectors[] = {
    {AUDIO_INPUT_SOURCE_CH1, MOD_LN_PN_SW_1_INDEX_CHANNEL0_ADDR, MOD_LN_PN_SW_1_INDEX_CHANNEL0_MEM_PAGE},
    {AUDIO_INPUT_SOURCE_CH2, MOD_LN_PN_SW_2_INDEX_CHANNEL0_ADDR, MOD_LN_PN_SW_2_INDEX_CHANNEL0_MEM_PAGE},
};

static const adau1466_safeload_selector_t s_insert_selectors[] = {
    {AUDIO_INPUT_SOURCE_CH1, MOD_DVS_SW_1_INDEX_CHANNEL0_ADDR, MOD_DVS_SW_1_INDEX_CHANNEL0_MEM_PAGE},
    {AUDIO_INPUT_SOURCE_CH2, MOD_DVS_SW_2_INDEX_CHANNEL0_ADDR, MOD_DVS_SW_2_INDEX_CHANNEL0_MEM_PAGE},
};

static const adau1466_sample_rate_cfg_t s_sample_rate_cfgs[] = {
    {48000U, 0x06U, ADAU1466_SOUT0_FROM_ASRC2, ADAU1466_SOUT1_FROM_ASRC3, ADAU1466_USB_MUX_ASRC},
    {96000U, 0x03U, ADAU1466_SOUT_FROM_DSP, ADAU1466_SOUT_FROM_DSP, ADAU1466_USB_MUX_DIRECT},
};

enum
{
    ADAU1466_SAMPLE_RATE_CFG_COUNT = sizeof(s_sample_rate_cfgs) / sizeof(s_sample_rate_cfgs[0]),
    ADAU1466_SEND_SOURCE_COUNT = sizeof(s_send_source_addr) / sizeof(s_send_source_addr[0]),
    ADAU1466_SELECTOR_COUNT = sizeof(s_input_type_selectors) / sizeof(s_input_type_selectors[0]),
};

_Static_assert((sizeof(s_usb_gain_addr) / sizeof(s_usb_gain_addr[0])) == ADAU1466_USB_CH_COUNT,
               "USB gain table must cover all USB channels");
_Static_assert((sizeof(s_usb_mute_addr) / sizeof(s_usb_mute_addr[0])) == ADAU1466_USB_CH_COUNT,
               "USB mute table must cover all USB channels");
_Static_assert((sizeof(s_input_type_selectors) / sizeof(s_input_type_selectors[0])) ==
               (sizeof(s_insert_selectors) / sizeof(s_insert_selectors[0])),
               "Input type and insert selector tables must cover the same channels");
_Static_assert(ADAU1466_CH_FADER_TARGET_COUNT == 3U, "Unexpected ch_fader target table size");

static float normalize_pot10_ratio(uint16_t adc_val)
{
    if (adc_val <= POT_10BIT_MIN_DEADZONE)
    {
        return 0.0f;
    }
    if (adc_val >= POT_10BIT_DB_MAX_SNAP_START)
    {
        return 1.0f;
    }

    return (float) (adc_val - POT_10BIT_MIN_DEADZONE) /
           (float) (POT_10BIT_DB_MAX_SNAP_START - POT_10BIT_MIN_DEADZONE);
}

static float normalize_pot10_snap_ratio(uint16_t adc_val)
{
    if (adc_val <= POT_10BIT_MIN_DEADZONE)
    {
        return 0.0f;
    }
    if (adc_val >= POT_10BIT_DW_MAX_SNAP_START)
    {
        return 1.0f;
    }

    return (float) (adc_val - POT_10BIT_MIN_DEADZONE) /
           (float) (POT_10BIT_DW_MAX_SNAP_START - POT_10BIT_MIN_DEADZONE);
}

static bool adau1466_get_sample_rate_cfg(uint32_t hz, adau1466_sample_rate_cfg_t* cfg)
{
    if (cfg == NULL)
    {
        return false;
    }

    for (uint32_t i = 0U; i < ADAU1466_SAMPLE_RATE_CFG_COUNT; i++)
    {
        if (s_sample_rate_cfgs[i].hz == hz)
        {
            *cfg = s_sample_rate_cfgs[i];
            return true;
        }
    }

    return false;
}

static bool adau1466_audio_input_source_to_mux_index(adau1466_input_source_t audio_input_source,
                                                     uint8_t* mux_index)
{
    if (mux_index == NULL)
    {
        return false;
    }

    switch (audio_input_source)
    {
    case AUDIO_INPUT_SOURCE_CH1:
        *mux_index = 0U;
        return true;
    case AUDIO_INPUT_SOURCE_CH2:
        *mux_index = 1U;
        return true;
    case AUDIO_INPUT_SOURCE_USB12:
        *mux_index = 2U;
        return true;
    case AUDIO_INPUT_SOURCE_USB34:
        *mux_index = 3U;
        return true;
    default:
        return false;
    }
}

static bool adau1466_return_source_to_mux_index(adau1466_input_source_t audio_input_source,
                                                uint8_t* mux_index)
{
    if (mux_index == NULL)
    {
        return false;
    }

    switch (audio_input_source)
    {
    case AUDIO_INPUT_SOURCE_USB12:
        *mux_index = 0U;
        return true;
    case AUDIO_INPUT_SOURCE_USB34:
        *mux_index = 1U;
        return true;
    default:
        return false;
    }
}

static bool adau1466_hp_source_to_mux_index(adau1466_hp_source_t hp_source, uint8_t* mux_index)
{
    if (mux_index == NULL)
    {
        return false;
    }

    switch (hp_source)
    {
    case HP_SOURCE_CH_FADER_A:
        *mux_index = 0U;
        return true;
    case HP_SOURCE_CH_FADER_B:
        *mux_index = 1U;
        return true;
    case HP_SOURCE_THRU:
        *mux_index = 2U;
        return true;
    case HP_SOURCE_MASTER:
        *mux_index = 3U;
        return true;
    default:
        return false;
    }
}

static bool adau1466_write_reg_u16(uint16_t addr, uint8_t value, sigma_spi_call_detail_t* detail)
{
    uint8_t data[2] = {0x00, value};

    if (sigma_spi_write_block(DEVICE_ADDR_ADAU146XSCHEMATIC_1, addr, 2, data, detail) != SIGMA_SPI_RESULT_OK)
    {
        SEGGER_RTT_printf(0, "[ADAU1466] register write failed: addr=%u\n", (unsigned) addr);
        return false;
    }

    return true;
}

// PLLロック待ちの結果。SPI読み出し失敗とロック待ちタイムアウトを区別する。
typedef enum
{
    ADAU1466_PLL_WAIT_LOCKED = 0,
    ADAU1466_PLL_WAIT_TIMEOUT,
    ADAU1466_PLL_WAIT_SPI_FAILED,
} adau1466_pll_wait_result_t;

static adau1466_pll_wait_result_t adau1466_wait_pll_lock(uint32_t timeout_ms,
                                                         sigma_spi_call_detail_t* detail)
{
    uint8_t pll_lock[2] = {0};
    uint32_t start_tick = HAL_GetTick();

    while ((HAL_GetTick() - start_tick) < timeout_ms)
    {
        if (sigma_spi_read_register(DEVICE_ADDR_ADAU146XSCHEMATIC_1, ADAU1466_REG_PLL_LOCK, 2, pll_lock,
                                    detail) != SIGMA_SPI_RESULT_OK)
        {
            // 読出し失敗を「PLL未lock」や過去の受信値と混同しない。
            SEGGER_RTT_printf(0, "[ADAU1466] PLL lock read failed\n");
            return ADAU1466_PLL_WAIT_SPI_FAILED;
        }
        if ((pll_lock[1] & 0x01U) != 0U)
        {
            return ADAU1466_PLL_WAIT_LOCKED;
        }
        osDelay(1);
    }

    SEGGER_RTT_printf(0, "[ADAU1466] PLL lock timeout\n");
    return ADAU1466_PLL_WAIT_TIMEOUT;
}

static uint32_t adau1466_q8_24_to_raw(double val)
{
    int64_t fixed_q8_24 = (int64_t) llround(val * 16777216.0);  // 2^24
    if (fixed_q8_24 > INT32_MAX)
    {
        fixed_q8_24 = INT32_MAX;
    }
    else if (fixed_q8_24 < INT32_MIN)
    {
        fixed_q8_24 = INT32_MIN;
    }

    return (uint32_t) ((int32_t) fixed_q8_24);
}

static void adau1466_store_be32(uint32_t raw, uint8_t out[4])
{
    out[0] = (uint8_t) ((raw >> 24) & 0xFFU);
    out[1] = (uint8_t) ((raw >> 16) & 0xFFU);
    out[2] = (uint8_t) ((raw >> 8) & 0xFFU);
    out[3] = (uint8_t) (raw & 0xFFU);
}

static void adau1466_delay_us(uint32_t delay_us)
{
    if (delay_us == 0U)
    {
        return;
    }

    if (((CoreDebug->DEMCR & CoreDebug_DEMCR_TRCENA_Msk) == 0U) ||
        ((DWT->CTRL & DWT_CTRL_CYCCNTENA_Msk) == 0U))
    {
        HAL_Delay((delay_us + 999U) / 1000U);
        return;
    }

    uint32_t cycles_per_us = HAL_RCC_GetHCLKFreq() / 1000000U;
    if (cycles_per_us == 0U)
    {
        HAL_Delay(1);
        return;
    }

    uint32_t start_cycle = DWT->CYCCNT;
    uint32_t wait_cycles = cycles_per_us * delay_us;

    while ((DWT->CYCCNT - start_cycle) < wait_cycles)
    {
    }
}

static void adau1466_wait_safeload_frame(void)
{
    adau1466_delay_us((1000000U + ADAU1466_CORE_SAMPLE_RATE_HZ - 1U) /
                      ADAU1466_CORE_SAMPLE_RATE_HZ);
}

static bool adau1466_safeload_write_words(uint16_t addr, uint8_t mem_page, const uint8_t* data, uint8_t word_count,
                                          sigma_spi_call_detail_t* detail)
{
    uint8_t safeload_ctrl[12] = {0x00};

    if ((data == NULL) || (word_count == 0U) || (word_count > 5U))
    {
        SEGGER_RTT_printf(0, "[ADAU1466] invalid safeload word_count: %u\n", word_count);
        if (detail != NULL)
        {
            detail->result = SIGMA_SPI_RESULT_INVALID_ARG;
        }
        return false;
    }

    if (mem_page > 1U)
    {
        SEGGER_RTT_printf(0, "[ADAU1466] invalid safeload mem_page: %u\n", mem_page);
        if (detail != NULL)
        {
            detail->result = SIGMA_SPI_RESULT_INVALID_ARG;
        }
        return false;
    }

    adau1466_store_be32(addr, &safeload_ctrl[0]);
    if (mem_page == 0U)
    {
        safeload_ctrl[7] = word_count;
    }
    else
    {
        safeload_ctrl[11] = word_count;
    }

    // data準備→control/commit書込み→DSP frame待ちを一つの排他単位にする。
    const sigma_spi_result_t begin = sigma_spi_safeload_begin(detail);
    if (begin != SIGMA_SPI_RESULT_OK)
    {
        SEGGER_RTT_printf(0, "[ADAU1466] safeload lock failed: %u\n", (unsigned) begin);
        return false;
    }

    sigma_spi_result_t result = sigma_spi_safeload_write_locked(
        DEVICE_ADDR_ADAU146XSCHEMATIC_1, MOD_SAFELOAD_DATA_SAFELOAD0_ADDR, (uint16_t) (word_count * 4U), (uint8_t*) data,
        detail);

    if (result == SIGMA_SPI_RESULT_OK)
    {
        result = sigma_spi_safeload_write_locked(
            DEVICE_ADDR_ADAU146XSCHEMATIC_1, MOD_SAFELOAD_ADDR_SAFELOAD_ADDR, sizeof(safeload_ctrl), safeload_ctrl,
            detail);
    }

    if (result != SIGMA_SPI_RESULT_OK)
    {
        // data書込み失敗時はcontrol/commitを送らない。control失敗時も成功を返さない。
        sigma_spi_safeload_end();
        SEGGER_RTT_printf(0,
                          "[ADAU1466] safeload write failed: addr=%u result=%u\n",
                          (unsigned) addr,
                          (unsigned) result);
        return false;
    }

    // 後続Safeloadがscratch領域へ割り込まないよう、既存のframe待ちも排他内で行う。
    adau1466_wait_safeload_frame();
    sigma_spi_safeload_end();

    return true;
}

double adau1466_convert_pot_to_db(uint16_t adc_val)
{
    double x  = (double) normalize_pot10_ratio(adc_val);
    double db = 0.0;
    if (x < 0.7)
    {
        db = -80.0 + (x / 0.7) * 80.0;
    }
    else
    {
        db = (x - 0.7) / 0.3 * 10.0;
    }
    return db;
}

int16_t adau1466_convert_pot_to_db_int(uint16_t adc_val)
{
    // Pot end-stop付近のADCノイズで表示/制御値が揺れないように端点デッドゾーンを設ける
    if (adc_val <= POT_10BIT_MIN_DEADZONE)
    {
        return -80;
    }
    if (adc_val >= POT_10BIT_DB_MAX_SNAP_START)
    {
        return 10;
    }

    double db    = adau1466_convert_pot_to_db(adc_val);
    int16_t db_i = (int16_t) ((db >= 0.0) ? (db + 0.5) : (db - 0.5));
    if (db_i < -80)
    {
        db_i = -80;
    }
    if (db_i > 10)
    {
        db_i = 10;
    }
    return db_i;
}

double adau1466_convert_db_to_gain(double db)
{
    return pow(10.0, db / 20.0);
}

// DSPへQ8.24値を書き込む。呼出側が適用成否を判定できるようSPI結果を返す。
static sigma_spi_result_t write_q8_24(const uint16_t addr, const double val)
{
    uint8_t gain_array[4] = {0x00};
    uint32_t raw          = adau1466_q8_24_to_raw(val);

    adau1466_store_be32(raw, gain_array);

    return sigma_spi_write_block_it(DEVICE_ADDR_ADAU146XSCHEMATIC_1, addr, 4, gain_array, NULL);
}

static void adau1466_write_indexed_q8_24(const uint16_t* addr_table, uint32_t count,
                                         uint32_t index, const double val)
{
    if ((addr_table == NULL) || (index >= count))
    {
        return;
    }

    write_q8_24(addr_table[index], val);
}

static void adau1466_write_pot_gain(uint16_t addr, uint16_t adc_val)
{
    const double db   = (double) adau1466_convert_pot_to_db_int(adc_val);
    const double gain = adau1466_convert_db_to_gain(db);
    write_q8_24(addr, gain);
}

static void adau1466_write_int_mux(uint16_t addr, uint8_t mux_index)
{
    uint8_t data[4] = {0x00U, 0x00U, 0x00U, mux_index};
    SIGMA_WRITE_REGISTER_BLOCK(DEVICE_ADDR_ADAU146XSCHEMATIC_1, addr, 4, data);
}

static void adau1466_write_int_mux_it(uint16_t addr, uint8_t mux_index)
{
    uint8_t data[4] = {0x00U, 0x00U, 0x00U, mux_index};
    SIGMA_WRITE_REGISTER_BLOCK_IT(DEVICE_ADDR_ADAU146XSCHEMATIC_1, addr, 4, data);
}

static bool adau1466_find_channel_addr(const adau1466_channel_addr_t* table, uint32_t count,
                                       adau1466_input_source_t audio_input_source, uint16_t* addr)
{
    if ((table == NULL) || (addr == NULL))
    {
        return false;
    }

    for (uint32_t i = 0U; i < count; i++)
    {
        if (table[i].channel == (uint8_t) audio_input_source)
        {
            *addr = table[i].addr;
            return true;
        }
    }

    return false;
}

static bool adau1466_find_selector(const adau1466_safeload_selector_t* table, uint32_t count,
                                   adau1466_input_source_t audio_input_source,
                                   const adau1466_safeload_selector_t** selector)
{
    if ((table == NULL) || (selector == NULL))
    {
        return false;
    }

    for (uint32_t i = 0U; i < count; i++)
    {
        if (table[i].channel == (uint8_t) audio_input_source)
        {
            *selector = &table[i];
            return true;
        }
    }

    return false;
}

static bool adau1466_write_two_way_safeload(const adau1466_safeload_selector_t* selector,
                                            uint8_t selected_index)
{
    uint8_t safeload_data[8] = {0x00};

    if ((selector == NULL) || (selected_index > 1U))
    {
        return false;
    }

    // One-hot in Q8.24 format: 1.0 in the selected word.
    safeload_data[(uint32_t) selected_index * 4U] = 0x01U;

    return adau1466_safeload_write_words(selector->addr, selector->mem_page, safeload_data, 2U, NULL);
}

static void adau1466_select_ch_fader_source(uint16_t addr, adau1466_input_source_t audio_input_source)
{
    uint8_t mux_index = 0U;

    // Existing behavior: an invalid source still writes index 0 (the previous
    // zero-initialized payload value). Do not change it in this refactoring.
    (void) adau1466_audio_input_source_to_mux_index(audio_input_source, &mux_index);
    adau1466_write_int_mux(addr, mux_index);
}

void adau1466_safeload_write_q8_24(uint16_t addr, uint8_t mem_page, double val)
{
    uint8_t safeload_data[4] = {0x00};
    adau1466_store_be32(adau1466_q8_24_to_raw(val), safeload_data);
    (void) adau1466_safeload_write_words(addr, mem_page, safeload_data, 1U, NULL);
}

bool adau1466_init_checked(uint32_t hz)
{
    // ADAU1466 HW Reset
    HAL_GPIO_WritePin(DSP_RESET_GPIO_Port, DSP_RESET_Pin, 0);
    osDelay(10);
    HAL_GPIO_WritePin(DSP_RESET_GPIO_Port, DSP_RESET_Pin, 1);
    osDelay(500);

#if RESET_FROM_FW
    // Program/configuration download is required only after reset. Runtime
    // sample-rate changes keep the 96 kHz DSP program and parameters intact.
    default_download_ADAU146XSCHEMATIC_1();
    osDelay(5);
#endif

    if (!adau1466_update_sample_rate(hz))
    {
        SEGGER_RTT_printf(0, "[ADAU1466] initialization failed for %lu Hz\n", (unsigned long) hz);
        return false;
    }

    return true;
}

void adau1466_init(uint32_t hz)
{
    (void) adau1466_init_checked(hz);
}

// DSPレート適用の失敗理由を記録する。SPI結果・HAL結果は失敗した呼出し固有の
// detail（共有診断の後読みではない）から取得する。
static void adau1466_rate_failure_record(adau1466_rate_failure_t* failure,
                                         adau1466_rate_fail_t reason,
                                         adau1466_rate_step_t step,
                                         const sigma_spi_call_detail_t* detail)
{
    if (failure == NULL)
    {
        return;
    }

    failure->reason           = reason;
    failure->step             = step;
    failure->spi_result       = (detail != NULL) ? (uint32_t) detail->result : 0u;
    failure->spi_hal_status   = (detail != NULL) ? detail->hal_status : 0u;
    failure->spi_hal_error    = (detail != NULL) ? detail->hal_error : 0u;
    failure->spi_abort_status = (detail != NULL) ? detail->abort_status : 0u;
}

bool adau1466_update_sample_rate_checked(uint32_t hz, adau1466_rate_failure_t* failure)
{
    adau1466_sample_rate_cfg_t cfg;

    if (failure != NULL)
    {
        failure->reason           = ADAU1466_RATE_FAIL_NONE;
        failure->step             = ADAU1466_RATE_STEP_NONE;
        failure->spi_result       = 0u;
        failure->spi_hal_status   = 0u;
        failure->spi_hal_error    = 0u;
        failure->spi_abort_status = 0u;
    }

    if (!adau1466_get_sample_rate_cfg(hz, &cfg))
    {
        SEGGER_RTT_printf(0, "[ADAU1466] unsupported sample rate: %lu\n", (unsigned long) hz);
        if (failure != NULL)
        {
            failure->reason = ADAU1466_RATE_FAIL_UNSUPPORTED;
        }
        return false;
    }

    uint8_t mux_data[4] = {0U};
    uint8_t sout_data[4] = {0x00U, cfg.sout_source0, 0x00U, cfg.sout_source1};
    adau1466_store_be32(cfg.usb_mux_index, mux_data);
    sigma_spi_call_detail_t detail = {0};

    if (hz == 48000U)
    {
        // Move both DSP paths to the ASRCs while the serial port still runs at
        // 96 kHz, then lower only the USB-side clock generator to 48 kHz.
        if (!adau1466_safeload_write_words(MOD_USB_RATE_SELECT_INDEX4_ADDR,
                                           MOD_USB_RATE_SELECT_INDEX4_MEM_PAGE,
                                           mux_data,
                                           1U,
                                           &detail))
        {
            adau1466_rate_failure_record(failure, ADAU1466_RATE_FAIL_SPI,
                                         ADAU1466_RATE_STEP_MUX, &detail);
            return false;
        }
        if (sigma_spi_write_block(DEVICE_ADDR_ADAU146XSCHEMATIC_1,
                                  ADAU1466_REG_SOUT_SOURCE0,
                                  sizeof(sout_data),
                                  sout_data,
                                  &detail) != SIGMA_SPI_RESULT_OK)
        {
            SEGGER_RTT_printf(0, "[ADAU1466] SOUT source write failed\n");
            adau1466_rate_failure_record(failure, ADAU1466_RATE_FAIL_SPI,
                                         ADAU1466_RATE_STEP_SOUT_SOURCE, &detail);
            return false;
        }
        if (!adau1466_write_reg_u16(ADAU1466_REG_CLK_GEN2_M, cfg.clk_gen2_m, &detail))
        {
            adau1466_rate_failure_record(failure, ADAU1466_RATE_FAIL_SPI,
                                         ADAU1466_RATE_STEP_CLK_GEN, &detail);
            return false;
        }
    }
    else
    {
        // Bring the USB-side serial port to 96 kHz before selecting the direct
        // paths. The DSP core and AK4619 clocks remain at 96 kHz throughout.
        if (!adau1466_write_reg_u16(ADAU1466_REG_CLK_GEN2_M, cfg.clk_gen2_m, &detail))
        {
            adau1466_rate_failure_record(failure, ADAU1466_RATE_FAIL_SPI,
                                         ADAU1466_RATE_STEP_CLK_GEN, &detail);
            return false;
        }
        osDelay(ADAU1466_CLOCK_SETTLE_MS);
        if (!adau1466_safeload_write_words(MOD_USB_RATE_SELECT_INDEX4_ADDR,
                                           MOD_USB_RATE_SELECT_INDEX4_MEM_PAGE,
                                           mux_data,
                                           1U,
                                           &detail))
        {
            adau1466_rate_failure_record(failure, ADAU1466_RATE_FAIL_SPI,
                                         ADAU1466_RATE_STEP_MUX, &detail);
            return false;
        }
        if (sigma_spi_write_block(DEVICE_ADDR_ADAU146XSCHEMATIC_1,
                                  ADAU1466_REG_SOUT_SOURCE0,
                                  sizeof(sout_data),
                                  sout_data,
                                  &detail) != SIGMA_SPI_RESULT_OK)
        {
            SEGGER_RTT_printf(0, "[ADAU1466] SOUT source write failed\n");
            adau1466_rate_failure_record(failure, ADAU1466_RATE_FAIL_SPI,
                                         ADAU1466_RATE_STEP_SOUT_SOURCE, &detail);
            return false;
        }
    }

    osDelay(ADAU1466_CLOCK_SETTLE_MS);

    const adau1466_pll_wait_result_t pll_wait = adau1466_wait_pll_lock(ADAU1466_PLL_LOCK_TIMEOUT_MS, &detail);
    if (pll_wait != ADAU1466_PLL_WAIT_LOCKED)
    {
        // SPI読み出し失敗とロック待ちタイムアウトを区別して返す。
        const adau1466_rate_fail_t reason = (pll_wait == ADAU1466_PLL_WAIT_SPI_FAILED) ?
                                                ADAU1466_RATE_FAIL_SPI : ADAU1466_RATE_FAIL_PLL_TIMEOUT;
        adau1466_rate_failure_record(failure, reason, ADAU1466_RATE_STEP_PLL_READ, &detail);
        return false;
    }

    SEGGER_RTT_printf(0,
                      "[ADAU1466] USB path: %lu Hz, CLK_GEN2 M=%u, %s\n",
                      (unsigned long) hz,
                      cfg.clk_gen2_m,
                      (cfg.usb_mux_index == ADAU1466_USB_MUX_ASRC) ? "ASRC" : "direct");
    return true;
}

bool adau1466_update_sample_rate(uint32_t hz)
{
    return adau1466_update_sample_rate_checked(hz, NULL);
}

void adau1466_set_dc_input_a(float ch_fader_position)
{
    adau1466_write_indexed_q8_24(s_dc_input_addr, ADAU1466_DC_INPUT_COUNT,
                                 ADAU1466_DC_INPUT_A, ch_fader_position);
}

void adau1466_set_dc_input_b(float ch_fader_position)
{
    adau1466_write_indexed_q8_24(s_dc_input_addr, ADAU1466_DC_INPUT_COUNT,
                                 ADAU1466_DC_INPUT_B, ch_fader_position);
}

sigma_spi_result_t adau1466_control_input_from_usb_gain(uint8_t ch, int16_t db)
{
    SEGGER_RTT_printf(0, "USB CH%d Gain: %d dB\n", ch, db);

    if ((ch < 1U) || ((uint16_t) ch > ADAU1466_USB_CH_COUNT))
    {
        return SIGMA_SPI_RESULT_INVALID_ARG;
    }

    return write_q8_24(s_usb_gain_addr[(uint32_t) ch - 1U], adau1466_convert_db_to_gain(db));
}

sigma_spi_result_t adau1466_control_input_from_usb_mute(uint8_t ch, bool muted)
{
    if ((ch < 1U) || ((uint16_t) ch > ADAU1466_USB_CH_COUNT))
    {
        return SIGMA_SPI_RESULT_INVALID_ARG;
    }

    SEGGER_RTT_printf(0, "USB CH%d Mute: %d\n", ch, muted ? 1 : 0);
    return write_q8_24(s_usb_mute_addr[(uint32_t) ch - 1U], muted ? 0.0 : 1.0);
}

void adau1466_control_input_from_ch1_gain(const uint16_t adc_val)
{
    adau1466_write_pot_gain(MOD_INPUT_FROM_CH1_GAIN_ADDR, adc_val);
}

void adau1466_control_input_from_ch2_gain(const uint16_t adc_val)
{
    adau1466_write_pot_gain(MOD_INPUT_FROM_CH2_GAIN_ADDR, adc_val);
}

void adau1466_control_input_from_return_gain(const uint16_t adc_val)
{
    adau1466_write_pot_gain(MOD_INPUT_FROM_RETURN_GAIN_ADDR, adc_val);
}

void adau1466_mute_input_from_return(void)
{
    write_q8_24(MOD_INPUT_FROM_RETURN_GAIN_ADDR, 0.0);
}

void adau1466_control_send1_out_gain(const uint16_t adc_val)
{
    adau1466_write_pot_gain(MOD_SEND1_OUTPUT_GAIN_ADDR, adc_val);
}

void adau1466_control_send2_out_gain(const uint16_t adc_val)
{
    adau1466_write_pot_gain(MOD_SEND2_OUTPUT_GAIN_ADDR, adc_val);
}

void adau1466_control_dry_a_out_gain(const uint16_t adc_val)
{
    const float rate = cos(pow(normalize_pot10_snap_ratio(adc_val), 2.0f) * M_PI_2);
    adau1466_write_indexed_q8_24(s_dry_dc_addr, ADAU1466_DRY_DC_COUNT,
                                 ADAU1466_DRY_DC_A, rate);
}

void adau1466_control_dry_b_out_gain(const uint16_t adc_val)
{
    const float rate = cos(pow(normalize_pot10_snap_ratio(adc_val), 2.0f) * M_PI_2);
    adau1466_write_indexed_q8_24(s_dry_dc_addr, ADAU1466_DRY_DC_COUNT,
                                 ADAU1466_DRY_DC_B, rate);
}

void adau1466_control_wet_out_gain(const uint16_t adc_val)
{
    const float rate = sin(pow(normalize_pot10_snap_ratio(adc_val), 2.0f) * M_PI_2);
    write_q8_24(MOD_DCINPUT_WET_DCVALUE_ADDR, rate);
}

void adau1466_control_ch1_out_gain(const uint16_t adc_val)
{
    adau1466_write_pot_gain(MOD_CH1_OUTPUT_GAIN_ADDR, adc_val);
}

void adau1466_control_ch2_out_gain(const uint16_t adc_val)
{
    adau1466_write_pot_gain(MOD_CH2_OUTPUT_GAIN_ADDR, adc_val);
}

void adau1466_control_hp_out_gain(const uint16_t adc_val)
{
    adau1466_write_pot_gain(MOD_HP_OUTPUT_GAIN_ADDR, adc_val);
}

void adau1466_select_input_type(adau1466_input_source_t audio_input_source, uint8_t input_type)
{
    const adau1466_safeload_selector_t* selector;

    if ((input_type != INPUT_TYPE_LINE) && (input_type != INPUT_TYPE_PHONO))
    {
        return;
    }

    if (!adau1466_find_selector(s_input_type_selectors, ADAU1466_SELECTOR_COUNT,
                                audio_input_source, &selector))
    {
        return;
    }

    (void) adau1466_write_two_way_safeload(selector, (input_type == INPUT_TYPE_PHONO) ? 1U : 0U);
}

void adau1466_set_input_insert_enabled(adau1466_input_source_t audio_input_source, bool enabled)
{
    const adau1466_safeload_selector_t* selector;

    if (!adau1466_find_selector(s_insert_selectors, ADAU1466_SELECTOR_COUNT,
                                audio_input_source, &selector))
    {
        return;
    }

    (void) adau1466_write_two_way_safeload(selector, enabled ? 1U : 0U);
}

void adau1466_select_send_source(adau1466_input_source_t audio_input_source, bool select_insert)
{
    uint16_t addr;

    if (!adau1466_find_channel_addr(s_send_source_addr, ADAU1466_SEND_SOURCE_COUNT,
                                    audio_input_source, &addr))
    {
        return;
    }

    adau1466_write_int_mux_it(addr, select_insert ? 1U : 0U);
}

void adau1466_select_ch_fader_assign_a_source(adau1466_input_source_t audio_input_source)
{
    adau1466_select_ch_fader_source(s_ch_fader_assign_addr[ADAU1466_CH_FADER_TARGET_A],
                                    audio_input_source);
}

void adau1466_select_ch_fader_assign_b_source(adau1466_input_source_t audio_input_source)
{
    adau1466_select_ch_fader_source(s_ch_fader_assign_addr[ADAU1466_CH_FADER_TARGET_B],
                                    audio_input_source);
}

void adau1466_select_ch_fader_assign_post_source(adau1466_input_source_t audio_input_source)
{
    adau1466_select_ch_fader_source(s_ch_fader_assign_addr[ADAU1466_CH_FADER_TARGET_POST],
                                    audio_input_source);
}

void adau1466_select_return_ch_source(adau1466_input_source_t audio_input_source)
{
    uint8_t mux_index;

    if (!adau1466_return_source_to_mux_index(audio_input_source, &mux_index))
    {
        return;
    }

    adau1466_write_int_mux(MOD_RETURN_CH_SW_INDEX_ADDR, mux_index);
}

void adau1466_select_hp_out_source(adau1466_hp_source_t hp_source)
{
    uint8_t mux_index = 0U;

    // Existing behavior: an invalid source still writes index 0 (the previous
    // zero-initialized payload value). Do not change it in this refactoring.
    (void) adau1466_hp_source_to_mux_index(hp_source, &mux_index);
    adau1466_write_int_mux(MOD_HP_OUT_SW_INDEX_ADDR, mux_index);
}
