yamamo2shun1/JUMBLEQ/STM32CubeIDE/JUMBLEQ/Appli/Core/Src/audio_diagnostics.c

/*
 * audio_diagnostics.c
 *
 * Audio diagnostics state, recording helpers and the periodic RTT summary.
 *
 * All record functions are called from ISR context and only update fixed-size
 * counters/min-max values. RTT output happens exclusively in the Audio Task
 * through audio_diagnostics_log_periodic() and audio_diagnostics_report_dma_time().
 */

#include "audio_diagnostics_internal.h"

#include "SEGGER_RTT.h"
#include "stm32h7rsxx_hal.h"

#include "SigmaStudioFW.h"

#define DBG_MIN_U32_INIT UINT32_MAX

enum
{
    DBG_MIN_U16_INIT = 0xFFFFu,
    AUDIO_USB_HS_MICROFRAMES_PER_SECOND = 8000u,
};

volatile audio_tx_diagnostics_t g_audio_tx_diagnostics = {
    .tx_used_min_words = UINT32_MAX,
};

volatile audio_rx_diagnostics_t g_audio_rx_diagnostics = {0};
volatile audio_recovery_diagnostics_t g_audio_recovery_diagnostics = {0};
volatile audio_window_totals_t g_audio_window_totals = {0};
// デバッガがCPUのDキャッシュに依らずに読めるよう非キャッシュ領域に置く（NOLOADなので
// audio_diagnostics_snapshot_reset()で0にする）。
__attribute__((section("noncacheable_buffer"))) volatile audio_diagnostics_snapshot_t g_audio_diagnostics_snapshot;
// state=1はAudioRateState_tのSWITCHING（初期適用確認前）を表す。
volatile audio_rate_switch_diagnostics_t g_audio_rate_switch_diagnostics = {
    .state = 1u,
};

#if AUDIO_DIAG_LOG
static volatile uint32_t dbg_tx_used_min            = DBG_MIN_U32_INIT;
static volatile uint32_t dbg_tx_used_max            = 0u;
static volatile uint32_t dbg_tx_underrun_events     = 0u;
static volatile uint32_t dbg_tx_partial_fill_events = 0u;
static volatile uint32_t dbg_tx_drift_up_events     = 0u;
static volatile uint32_t dbg_tx_drift_dn_events     = 0u;
static volatile uint32_t dbg_dma_err_events         = 0u;
static volatile uint32_t dbg_sai_tx_err_events      = 0u;
static volatile uint32_t dbg_sai_rx_err_events      = 0u;
static volatile uint32_t dbg_sai_tx_last_err        = 0u;
static volatile uint32_t dbg_sai_rx_last_err        = 0u;
static volatile uint32_t dbg_sai_tx_sr_flags        = 0u;
static volatile uint32_t dbg_sai_rx_sr_flags        = 0u;
static uint32_t dbg_sigma_calls_prev                = 0u;
static uint32_t dbg_sigma_err_prev                  = 0u;
static uint32_t dbg_sigma_to_prev                   = 0u;
static uint32_t dbg_sigma_mto_prev                  = 0u;
static volatile uint32_t dbg_tx_half_rewrite_events = 0u;
static volatile uint32_t dbg_tx_cplt_rewrite_events = 0u;
static volatile uint32_t dbg_rx_half_rewrite_events = 0u;
static volatile uint32_t dbg_rx_cplt_rewrite_events = 0u;
static volatile uint32_t dbg_usb_out_fb_min         = DBG_MIN_U32_INIT;
static volatile uint32_t dbg_usb_out_fb_max         = 0u;
static volatile uint32_t dbg_usb_out_fb_last        = 0u;
static volatile uint32_t dbg_usb_out_packet_events  = 0u;
static volatile uint32_t dbg_usb_out_packet_bytes   = 0u;
static volatile uint16_t dbg_usb_out_packet_size_min = DBG_MIN_U16_INIT;
static volatile uint16_t dbg_usb_out_packet_size_max = 0u;
static volatile uint32_t dbg_usb_out_gap_cycles_min = DBG_MIN_U32_INIT;
static volatile uint32_t dbg_usb_out_gap_cycles_max = 0u;
static volatile uint32_t dbg_usb_out_gap_late_events = 0u;
static volatile uint32_t dbg_usb_out_prev_cycle     = 0u;
static volatile bool dbg_usb_out_prev_cycle_valid   = false;
static volatile uint16_t dbg_usb_out_fifo_min       = DBG_MIN_U16_INIT;
static volatile uint16_t dbg_usb_out_fifo_max       = 0u;
static volatile uint32_t dbg_usb_in_packet_events   = 0u;
static volatile uint32_t dbg_usb_in_packet_zero_events = 0u;
static volatile uint32_t dbg_usb_in_packet_bytes    = 0u;
static volatile uint16_t dbg_usb_in_packet_size_min = DBG_MIN_U16_INIT;
static volatile uint16_t dbg_usb_in_packet_size_max = 0u;
static volatile uint32_t dbg_usb_in_write_zero_events = 0u;
static volatile uint32_t dbg_usb_in_write_partial_events = 0u;
static volatile uint32_t dbg_usb_in_write_bytes     = 0u;
static volatile uint16_t dbg_usb_in_fifo_min        = DBG_MIN_U16_INIT;
static volatile uint16_t dbg_usb_in_fifo_max        = 0u;

static void audio_diagnostics_reset_interval_locked(void)
{
    dbg_tx_used_min            = DBG_MIN_U32_INIT;
    dbg_tx_used_max            = 0u;
    dbg_tx_underrun_events     = 0u;
    dbg_tx_partial_fill_events = 0u;
    dbg_tx_drift_up_events     = 0u;
    dbg_tx_drift_dn_events     = 0u;
    dbg_dma_err_events         = 0u;
    dbg_sai_tx_err_events      = 0u;
    dbg_sai_rx_err_events      = 0u;
    dbg_sai_tx_last_err        = 0u;
    dbg_sai_rx_last_err        = 0u;
    dbg_sai_tx_sr_flags        = 0u;
    dbg_sai_rx_sr_flags        = 0u;
    dbg_tx_half_rewrite_events = 0u;
    dbg_tx_cplt_rewrite_events = 0u;
    dbg_rx_half_rewrite_events = 0u;
    dbg_rx_cplt_rewrite_events = 0u;
    dbg_usb_out_fb_min         = DBG_MIN_U32_INIT;
    dbg_usb_out_fb_max         = 0u;
    dbg_usb_out_packet_events  = 0u;
    dbg_usb_out_packet_bytes   = 0u;
    dbg_usb_out_packet_size_min = DBG_MIN_U16_INIT;
    dbg_usb_out_packet_size_max = 0u;
    dbg_usb_out_gap_cycles_min = DBG_MIN_U32_INIT;
    dbg_usb_out_gap_cycles_max = 0u;
    dbg_usb_out_gap_late_events = 0u;
    dbg_usb_out_fifo_min       = DBG_MIN_U16_INIT;
    dbg_usb_out_fifo_max       = 0u;
    dbg_usb_in_packet_events   = 0u;
    dbg_usb_in_packet_zero_events = 0u;
    dbg_usb_in_packet_bytes    = 0u;
    dbg_usb_in_packet_size_min = DBG_MIN_U16_INIT;
    dbg_usb_in_packet_size_max = 0u;
    dbg_usb_in_write_zero_events = 0u;
    dbg_usb_in_write_partial_events = 0u;
    dbg_usb_in_write_bytes     = 0u;
    dbg_usb_in_fifo_min        = DBG_MIN_U16_INIT;
    dbg_usb_in_fifo_max        = 0u;
}
#endif

#if AUDIO_DIAG_LOG || AUDIO_DIAG_DMA_TIME_REPORT
static uint32_t audio_diagnostics_cycles_to_us(uint32_t cycles)
{
    if (SystemCoreClock == 0u)
    {
        return 0u;
    }

    return (uint32_t) ((((uint64_t) cycles * 1000000u) + (SystemCoreClock / 2u)) / SystemCoreClock);
}
#endif

void audio_diagnostics_reset_tx_locked(void)
{
    const uint32_t reset_count = g_audio_tx_diagnostics.reset_count + 1u;
    audio_tx_diagnostics_t reset = {0};
    reset.reset_count          = reset_count;
    reset.tx_used_min_words    = UINT32_MAX;
    g_audio_tx_diagnostics     = reset;
}

#if AUDIO_DIAG_LOG
void audio_diagnostics_reset_interval(void)
{
    const uint32_t primask = __get_PRIMASK();
    __disable_irq();

    audio_diagnostics_reset_interval_locked();

    __set_PRIMASK(primask);
}

void audio_diagnostics_reset_session(void)
{
    const uint32_t primask = __get_PRIMASK();
    __disable_irq();

    audio_diagnostics_reset_interval_locked();
    dbg_usb_out_prev_cycle       = 0u;
    dbg_usb_out_prev_cycle_valid = false;
    dbg_usb_out_fb_last          = 0u;

    __set_PRIMASK(primask);
}

void audio_diagnostics_reset_usb_out_gap(void)
{
    dbg_usb_out_prev_cycle_valid = false;
}
#endif

void audio_diagnostics_record_tx_level(bool streaming, int32_t used)
{
    if (!streaming || used < 0)
    {
        return;
    }

    const uint32_t level = (uint32_t) used;
    if (level < g_audio_tx_diagnostics.tx_used_min_words)
    {
        g_audio_tx_diagnostics.tx_used_min_words = level;
    }
    if (level > g_audio_tx_diagnostics.tx_used_max_words)
    {
        g_audio_tx_diagnostics.tx_used_max_words = level;
    }
}

#if AUDIO_DIAG_LOG
void audio_diagnostics_record_tx_interval_level(int32_t used)
{
    if (used < 0)
    {
        return;
    }

    const uint32_t level = (uint32_t) used;
    if (level < dbg_tx_used_min)
    {
        dbg_tx_used_min = level;
    }
    if (level > dbg_tx_used_max)
    {
        dbg_tx_used_max = level;
    }
}
#endif

void audio_diagnostics_record_tx_priming_wait(void)
{
    g_audio_tx_diagnostics.priming_wait_events++;
}

void audio_diagnostics_record_tx_priming_complete(void)
{
    g_audio_tx_diagnostics.priming_completed_events++;
}

void audio_diagnostics_record_out_stale_request_skip(void)
{
    g_audio_tx_diagnostics.out_stale_request_skips++;
}

void audio_diagnostics_record_out_fifo_full_event(void)
{
    g_audio_tx_diagnostics.out_fifo_full_events++;
}

void audio_diagnostics_record_out_fifo_overflow_recovery(uint32_t raw_count_bytes, uint32_t depth_bytes)
{
    g_audio_tx_diagnostics.out_fifo_overflow_recoveries++;
    // clearで破棄した有効データはdepthまで。raw countがdepthを超える分は上書き済み。
    g_audio_tx_diagnostics.out_fifo_overflow_discard_bytes +=
        (raw_count_bytes < depth_bytes) ? raw_count_bytes : depth_bytes;
    if (raw_count_bytes > depth_bytes)
    {
        // 観測できた上書き量。二重overflowで失われた分は含まれない（下限）。
        g_audio_tx_diagnostics.out_fifo_overflow_lost_bytes += raw_count_bytes - depth_bytes;
    }
    else
    {
        // ちょうど満杯。二重overflow後の可能性があり喪失量は不明。
        g_audio_tx_diagnostics.out_fifo_overflow_unknown_events++;
    }
}

void audio_diagnostics_record_out_reprime(void)
{
    g_audio_tx_diagnostics.out_reprime_events++;
}

void audio_diagnostics_record_out_take_section(uint32_t cycles)
{
    if (cycles > g_audio_tx_diagnostics.out_take_section_cycles_max)
    {
        g_audio_tx_diagnostics.out_take_section_cycles_max = cycles;
    }
}

void audio_diagnostics_record_tx_drift_threshold(bool upward)
{
    if (upward)
    {
        g_audio_tx_diagnostics.drift_up_threshold_events++;
    }
    else
    {
        g_audio_tx_diagnostics.drift_down_threshold_events++;
    }
}

void audio_diagnostics_record_tx_drift_suppressed(bool upward)
{
    if (upward)
    {
        g_audio_tx_diagnostics.drift_up_suppressed_events++;
    }
    else
    {
        g_audio_tx_diagnostics.drift_down_suppressed_events++;
    }
}

void audio_diagnostics_record_tx_event(bool streaming, uint32_t flags, int32_t used)
{
    if (streaming)
    {
        if ((flags & AUDIO_TX_DIAG_EVENT_UNDERRUN) != 0u)
        {
            g_audio_tx_diagnostics.underrun_events++;
            g_audio_window_totals.tx_underrun_events++;
        }
        if ((flags & AUDIO_TX_DIAG_EVENT_PARTIAL_FILL) != 0u)
        {
            g_audio_tx_diagnostics.partial_fill_events++;
        }
        if ((flags & AUDIO_TX_DIAG_EVENT_DRIFT_UP) != 0u)
        {
            g_audio_tx_diagnostics.drift_up_events++;
        }
        if ((flags & AUDIO_TX_DIAG_EVENT_DRIFT_DOWN) != 0u)
        {
            g_audio_tx_diagnostics.drift_down_events++;
        }

        g_audio_tx_diagnostics.last_event_used_words = used;
        g_audio_tx_diagnostics.last_event_flags      = flags;
        g_audio_tx_diagnostics.last_event_tick_ms    = HAL_GetTick();
        g_audio_tx_diagnostics.last_event_cycle      = DWT->CYCCNT;
    }

#if AUDIO_DIAG_LOG
    if ((flags & AUDIO_TX_DIAG_EVENT_UNDERRUN) != 0u)
    {
        dbg_tx_underrun_events++;
    }
    if ((flags & AUDIO_TX_DIAG_EVENT_PARTIAL_FILL) != 0u)
    {
        dbg_tx_partial_fill_events++;
    }
    if ((flags & AUDIO_TX_DIAG_EVENT_DRIFT_UP) != 0u)
    {
        dbg_tx_drift_up_events++;
    }
    if ((flags & AUDIO_TX_DIAG_EVENT_DRIFT_DOWN) != 0u)
    {
        dbg_tx_drift_dn_events++;
    }
#endif
}

void audio_diagnostics_record_tx_dma_callback(uint32_t callback_event,
                                              uint32_t overwritten_event,
                                              bool streaming,
                                              int32_t used)
{
    if (streaming)
    {
        if (callback_event == AUDIO_DIAG_DMA_EVENT_HALF)
        {
            g_audio_tx_diagnostics.tx_half_callbacks++;
        }
        else
        {
            g_audio_tx_diagnostics.tx_cplt_callbacks++;
        }

        if (overwritten_event == AUDIO_DIAG_DMA_EVENT_HALF)
        {
            g_audio_tx_diagnostics.half_rewrite_events++;
            audio_diagnostics_record_tx_event(true, AUDIO_TX_DIAG_EVENT_HALF_REWRITE, used);
        }
        else if (overwritten_event == AUDIO_DIAG_DMA_EVENT_COMPLETE)
        {
            g_audio_tx_diagnostics.cplt_rewrite_events++;
            audio_diagnostics_record_tx_event(true, AUDIO_TX_DIAG_EVENT_CPLT_REWRITE, used);
        }
        g_audio_tx_diagnostics.last_pending_callback = callback_event;
    }

#if AUDIO_DIAG_LOG
    if (overwritten_event == AUDIO_DIAG_DMA_EVENT_HALF)
    {
        dbg_tx_half_rewrite_events++;
    }
    else if (overwritten_event == AUDIO_DIAG_DMA_EVENT_COMPLETE)
    {
        dbg_tx_cplt_rewrite_events++;
    }
#endif
}

void audio_diagnostics_record_rx_dma_callback(uint32_t callback_event,
                                              uint32_t overwritten_event)
{
    if (callback_event == AUDIO_DIAG_DMA_EVENT_HALF)
    {
        g_audio_rx_diagnostics.rx_half_callbacks++;
    }
    else
    {
        g_audio_rx_diagnostics.rx_cplt_callbacks++;
    }

    if (overwritten_event == AUDIO_DIAG_DMA_EVENT_HALF)
    {
        g_audio_rx_diagnostics.rx_half_rewrite_events++;
    }
    else if (overwritten_event == AUDIO_DIAG_DMA_EVENT_COMPLETE)
    {
        g_audio_rx_diagnostics.rx_cplt_rewrite_events++;
    }

#if AUDIO_DIAG_LOG
    if (overwritten_event == AUDIO_DIAG_DMA_EVENT_HALF)
    {
        dbg_rx_half_rewrite_events++;
    }
    else if (overwritten_event == AUDIO_DIAG_DMA_EVENT_COMPLETE)
    {
        dbg_rx_cplt_rewrite_events++;
    }
#endif
}

void audio_diagnostics_record_tx_dma_service(uint32_t callback_event,
                                             uint32_t service_cycles,
                                             bool deadline_overrun)
{
    if (callback_event == AUDIO_DIAG_DMA_EVENT_HALF)
    {
        if (service_cycles > g_audio_tx_diagnostics.half_service_cycles_max)
        {
            g_audio_tx_diagnostics.half_service_cycles_max = service_cycles;
        }
        if (deadline_overrun)
        {
            g_audio_tx_diagnostics.half_deadline_overruns++;
        }
    }
    else if (callback_event == AUDIO_DIAG_DMA_EVENT_COMPLETE)
    {
        if (service_cycles > g_audio_tx_diagnostics.cplt_service_cycles_max)
        {
            g_audio_tx_diagnostics.cplt_service_cycles_max = service_cycles;
        }
        if (deadline_overrun)
        {
            g_audio_tx_diagnostics.cplt_deadline_overruns++;
        }
    }
}

void audio_diagnostics_record_rx_dma_service(uint32_t callback_event,
                                             uint32_t service_cycles,
                                             bool deadline_overrun)
{
    if (callback_event == AUDIO_DIAG_DMA_EVENT_HALF)
    {
        if (service_cycles > g_audio_rx_diagnostics.rx_half_service_cycles_max)
        {
            g_audio_rx_diagnostics.rx_half_service_cycles_max = service_cycles;
        }
        if (deadline_overrun)
        {
            g_audio_rx_diagnostics.rx_half_deadline_overruns++;
        }
    }
    else if (callback_event == AUDIO_DIAG_DMA_EVENT_COMPLETE)
    {
        if (service_cycles > g_audio_rx_diagnostics.rx_cplt_service_cycles_max)
        {
            g_audio_rx_diagnostics.rx_cplt_service_cycles_max = service_cycles;
        }
        if (deadline_overrun)
        {
            g_audio_rx_diagnostics.rx_cplt_deadline_overruns++;
        }
    }
}

// streaming中のcompleteが期限の半分以上か（50%未満の合格条件に使う）。期限なしは数えない。
static bool audio_diagnostics_complete_reaches_half_deadline(uint32_t complete_cycles, uint32_t deadline_cycles)
{
    return (deadline_cycles != UINT32_MAX) && (((uint64_t) complete_cycles * 2u) >= (uint64_t) deadline_cycles);
}

// DMA処理完了時間の記録。complete最大値の更新時に、そのイベントのdeadlineも
// 同時に保存する。deadline_cycles == UINT32_MAX（レート未確定）は期限超過に数えない。
void audio_diagnostics_record_tx_dma_complete(uint32_t callback_event,
                                              uint32_t process_cycles,
                                              uint32_t complete_cycles,
                                              uint32_t deadline_cycles,
                                              bool streaming)
{
    if (streaming)
    {
        g_audio_window_totals.tx_streaming_complete_events++;
        if (audio_diagnostics_complete_reaches_half_deadline(complete_cycles, deadline_cycles))
        {
            g_audio_window_totals.tx_streaming_complete_half_deadline_events++;
        }
    }

    if (callback_event == AUDIO_DIAG_DMA_EVENT_HALF)
    {
        if (process_cycles > g_audio_tx_diagnostics.half_process_cycles_max)
        {
            g_audio_tx_diagnostics.half_process_cycles_max = process_cycles;
        }
        if (complete_cycles > g_audio_tx_diagnostics.half_complete_cycles_max)
        {
            g_audio_tx_diagnostics.half_complete_cycles_max = complete_cycles;
            g_audio_tx_diagnostics.half_complete_deadline_cycles_at_max = deadline_cycles;
        }
        if (complete_cycles > deadline_cycles)
        {
            g_audio_tx_diagnostics.half_complete_deadline_overruns++;
            g_audio_window_totals.tx_half_complete_deadline_overruns++;
        }
    }
    else if (callback_event == AUDIO_DIAG_DMA_EVENT_COMPLETE)
    {
        if (process_cycles > g_audio_tx_diagnostics.cplt_process_cycles_max)
        {
            g_audio_tx_diagnostics.cplt_process_cycles_max = process_cycles;
        }
        if (complete_cycles > g_audio_tx_diagnostics.cplt_complete_cycles_max)
        {
            g_audio_tx_diagnostics.cplt_complete_cycles_max = complete_cycles;
            g_audio_tx_diagnostics.cplt_complete_deadline_cycles_at_max = deadline_cycles;
        }
        if (complete_cycles > deadline_cycles)
        {
            g_audio_tx_diagnostics.cplt_complete_deadline_overruns++;
            g_audio_window_totals.tx_cplt_complete_deadline_overruns++;
        }
    }

    g_audio_tx_diagnostics.last_process_cycles           = process_cycles;
    g_audio_tx_diagnostics.last_complete_cycles          = complete_cycles;
    g_audio_tx_diagnostics.last_complete_deadline_cycles = deadline_cycles;
}

void audio_diagnostics_record_rx_dma_complete(uint32_t callback_event,
                                              uint32_t process_cycles,
                                              uint32_t complete_cycles,
                                              uint32_t deadline_cycles,
                                              bool streaming)
{
    if (streaming)
    {
        g_audio_window_totals.rx_streaming_complete_events++;
        if (audio_diagnostics_complete_reaches_half_deadline(complete_cycles, deadline_cycles))
        {
            g_audio_window_totals.rx_streaming_complete_half_deadline_events++;
        }
    }

    if (callback_event == AUDIO_DIAG_DMA_EVENT_HALF)
    {
        if (process_cycles > g_audio_rx_diagnostics.rx_half_process_cycles_max)
        {
            g_audio_rx_diagnostics.rx_half_process_cycles_max = process_cycles;
        }
        if (complete_cycles > g_audio_rx_diagnostics.rx_half_complete_cycles_max)
        {
            g_audio_rx_diagnostics.rx_half_complete_cycles_max = complete_cycles;
            g_audio_rx_diagnostics.rx_half_complete_deadline_cycles_at_max = deadline_cycles;
        }
        if (complete_cycles > deadline_cycles)
        {
            g_audio_rx_diagnostics.rx_half_complete_deadline_overruns++;
        }
    }
    else if (callback_event == AUDIO_DIAG_DMA_EVENT_COMPLETE)
    {
        if (process_cycles > g_audio_rx_diagnostics.rx_cplt_process_cycles_max)
        {
            g_audio_rx_diagnostics.rx_cplt_process_cycles_max = process_cycles;
        }
        if (complete_cycles > g_audio_rx_diagnostics.rx_cplt_complete_cycles_max)
        {
            g_audio_rx_diagnostics.rx_cplt_complete_cycles_max = complete_cycles;
            g_audio_rx_diagnostics.rx_cplt_complete_deadline_cycles_at_max = deadline_cycles;
        }
        if (complete_cycles > deadline_cycles)
        {
            g_audio_rx_diagnostics.rx_cplt_complete_deadline_overruns++;
        }
    }

    g_audio_rx_diagnostics.rx_last_process_cycles           = process_cycles;
    g_audio_rx_diagnostics.rx_last_complete_cycles          = complete_cycles;
    g_audio_rx_diagnostics.rx_last_complete_deadline_cycles = deadline_cycles;
}

void audio_diagnostics_record_tx_events_dropped(uint32_t last_event,
                                                uint32_t dropped_events,
                                                int32_t used)
{
    g_audio_tx_diagnostics.both_pending_events++;
    g_audio_tx_diagnostics.dma_events_dropped += dropped_events;
    g_audio_window_totals.tx_dma_events_dropped += dropped_events;
    g_audio_tx_diagnostics.both_pending_last_callback = last_event;
    audio_diagnostics_record_tx_event(true, AUDIO_TX_DIAG_EVENT_BOTH_PENDING, used);
}

void audio_diagnostics_record_rx_events_dropped(uint32_t last_event,
                                                uint32_t dropped_events)
{
    g_audio_rx_diagnostics.rx_both_pending_events++;
    g_audio_rx_diagnostics.rx_dma_events_dropped += dropped_events;
    g_audio_rx_diagnostics.rx_both_pending_last_callback = last_event;
}

void audio_diagnostics_record_usb_in_start_boundary(uint32_t discarded_words)
{
    g_audio_rx_diagnostics.usb_in_start_boundaries++;
    g_audio_rx_diagnostics.usb_in_start_discard_words += discarded_words;
}

void audio_diagnostics_record_usb_in_fifo_level(uint32_t judged_count, uint32_t post_write_bound)
{
    if (judged_count > g_audio_rx_diagnostics.usb_in_fifo_judged_count_max)
    {
        g_audio_rx_diagnostics.usb_in_fifo_judged_count_max = judged_count;
    }
    if (post_write_bound > g_audio_rx_diagnostics.usb_in_fifo_post_write_max)
    {
        g_audio_rx_diagnostics.usb_in_fifo_post_write_max = post_write_bound;
    }
}

void audio_diagnostics_record_usb_in_fifo_trim(uint32_t trimmed_bytes)
{
    g_audio_rx_diagnostics.usb_in_fifo_trim_events++;
    g_audio_rx_diagnostics.usb_in_fifo_trim_bytes += trimmed_bytes;
}

void audio_diagnostics_record_usb_in_fifo_full_drop(void)
{
    g_audio_rx_diagnostics.usb_in_fifo_full_drops++;
}

void audio_diagnostics_record_usb_in_stale_request_skip(void)
{
    g_audio_rx_diagnostics.usb_in_stale_request_skips++;
}

void audio_diagnostics_record_usb_in_chunk_drop(uint32_t chunk_bytes)
{
    g_audio_rx_diagnostics.usb_in_chunk_drop_events++;
    g_audio_rx_diagnostics.usb_in_chunk_drop_bytes += chunk_bytes;
}

void audio_diagnostics_record_usb_in_write_error(bool partial)
{
    if (partial)
    {
        g_audio_rx_diagnostics.usb_in_write_partial_events++;
    }
    else
    {
        g_audio_rx_diagnostics.usb_in_write_zero_events++;
    }
}

void audio_diagnostics_record_usb_in_write_section(uint32_t cycles)
{
    if (cycles > g_audio_rx_diagnostics.usb_in_write_section_cycles_max)
    {
        g_audio_rx_diagnostics.usb_in_write_section_cycles_max = cycles;
    }
}

void audio_diagnostics_record_tx_dma_ownership(uint32_t result,
                                               uint32_t q,
                                               uint32_t suspend_cycles,
                                               bool over_budget,
                                               bool stale_flag_cleared,
                                               bool fault)
{
    switch (result)
    {
        case AUDIO_DIAG_DMA_OWN_OK:
            if (q > g_audio_tx_diagnostics.dma_commit_entry_q_max)
            {
                g_audio_tx_diagnostics.dma_commit_entry_q_max = q;
            }
            break;
        case AUDIO_DIAG_DMA_OWN_BUSY:
            g_audio_tx_diagnostics.dma_commit_skips++;
            g_audio_window_totals.tx_dma_commit_skips++;
            break;
        case AUDIO_DIAG_DMA_OWN_SUSPEND_TIMEOUT:
            g_audio_tx_diagnostics.dma_suspend_timeouts++;
            g_audio_window_totals.tx_dma_suspend_timeouts++;
            break;
        case AUDIO_DIAG_DMA_OWN_SUSPEND_FAULT:
            // ラッチ中の見送りは、新たに検出した回（fault）だけを数える。
            break;
        default:
            g_audio_tx_diagnostics.dma_commit_unknown_position_events++;
            g_audio_window_totals.tx_dma_commit_unknown_position_events++;
            break;
    }

    if (suspend_cycles > g_audio_tx_diagnostics.dma_suspend_cycles_max)
    {
        g_audio_tx_diagnostics.dma_suspend_cycles_max = suspend_cycles;
    }
    if (over_budget)
    {
        g_audio_tx_diagnostics.dma_suspend_over_budget_events++;
    }
    if (stale_flag_cleared)
    {
        g_audio_tx_diagnostics.dma_suspend_stale_flag_clears++;
        g_audio_window_totals.tx_dma_suspend_stale_flag_clears++;
    }
    if (fault)
    {
        g_audio_tx_diagnostics.dma_suspend_faults++;
        g_audio_window_totals.tx_dma_suspend_faults++;
    }
}

void audio_diagnostics_record_rx_dma_ownership(uint32_t result,
                                               uint32_t q,
                                               uint32_t suspend_cycles,
                                               bool over_budget,
                                               bool stale_flag_cleared,
                                               bool fault)
{
    switch (result)
    {
        case AUDIO_DIAG_DMA_OWN_OK:
            if (q > g_audio_rx_diagnostics.rx_dma_snapshot_entry_q_max)
            {
                g_audio_rx_diagnostics.rx_dma_snapshot_entry_q_max = q;
            }
            break;
        case AUDIO_DIAG_DMA_OWN_BUSY:
            g_audio_rx_diagnostics.rx_dma_snapshot_rejects++;
            break;
        case AUDIO_DIAG_DMA_OWN_SUSPEND_TIMEOUT:
            g_audio_rx_diagnostics.rx_dma_suspend_timeouts++;
            break;
        case AUDIO_DIAG_DMA_OWN_SUSPEND_FAULT:
        case AUDIO_DIAG_DMA_OWN_NOT_READY:
            // NOT_READYはやり直しの前の回。audio_diagnostics_record_rx_dma_not_ready()で数える。
            break;
        default:
            g_audio_rx_diagnostics.rx_dma_snapshot_unknown_position_events++;
            break;
    }

    if (suspend_cycles > g_audio_rx_diagnostics.rx_dma_suspend_cycles_max)
    {
        g_audio_rx_diagnostics.rx_dma_suspend_cycles_max = suspend_cycles;
    }
    if (over_budget)
    {
        g_audio_rx_diagnostics.rx_dma_suspend_over_budget_events++;
    }
    if (stale_flag_cleared)
    {
        g_audio_rx_diagnostics.rx_dma_suspend_stale_flag_clears++;
    }
    if (fault)
    {
        g_audio_rx_diagnostics.rx_dma_suspend_faults++;
    }
}

void audio_diagnostics_record_tx_dma_stream_boundary(void)
{
    g_audio_tx_diagnostics.dma_commit_stream_boundary_events++;
    g_audio_window_totals.tx_dma_commit_stream_boundary_events++;
}

void audio_diagnostics_record_rx_dma_fifo(uint32_t fifol_raw, bool fifo_valid, bool config_mismatch)
{
    if (fifo_valid)
    {
        if (fifol_raw > g_audio_rx_diagnostics.rx_dma_snapshot_fifol_max)
        {
            g_audio_rx_diagnostics.rx_dma_snapshot_fifol_max = fifol_raw;
        }
        if (fifol_raw > 2u)
        {
            g_audio_rx_diagnostics.rx_dma_snapshot_fifol_over_capacity_events++;
        }
    }
    if (config_mismatch)
    {
        g_audio_rx_diagnostics.rx_dma_snapshot_config_mismatch_events++;
    }
}

void audio_diagnostics_record_rx_dma_not_ready(uint32_t wait_cycles)
{
    g_audio_rx_diagnostics.rx_dma_snapshot_not_ready_events++;
    if (wait_cycles > g_audio_rx_diagnostics.rx_dma_snapshot_wait_cycles_max)
    {
        g_audio_rx_diagnostics.rx_dma_snapshot_wait_cycles_max = wait_cycles;
    }
}

void audio_diagnostics_record_dma_error(uint32_t error_code,
                                        bool tx_route,
                                        bool streaming,
                                        int32_t used)
{
    if (tx_route)
    {
        g_audio_tx_diagnostics.dma_error_events++;
        g_audio_window_totals.tx_dma_error_events++;
        g_audio_tx_diagnostics.last_dma_error_code = error_code;
        audio_diagnostics_record_tx_event(streaming, AUDIO_TX_DIAG_EVENT_DMA_ERROR, used);
    }
    else
    {
        g_audio_rx_diagnostics.dma_error_events++;
        g_audio_rx_diagnostics.last_dma_error_code = error_code;
    }
#if AUDIO_DIAG_LOG
    dbg_dma_err_events++;
#endif
}

void audio_diagnostics_record_unknown_dma_error(uint32_t error_code)
{
    g_audio_recovery_diagnostics.unknown_dma_error_events++;
    g_audio_recovery_diagnostics.last_unknown_dma_error_code = error_code;
}

void audio_diagnostics_record_sai_tx_error(uint32_t error_code,
                                           uint32_t status_flags,
                                           bool streaming,
                                           int32_t used)
{
    g_audio_tx_diagnostics.sai_error_events++;
    g_audio_window_totals.tx_sai_error_events++;
    g_audio_tx_diagnostics.last_sai_error_code   = error_code;
    g_audio_tx_diagnostics.last_sai_status_flags = status_flags;
    audio_diagnostics_record_tx_event(streaming, AUDIO_TX_DIAG_EVENT_SAI_ERROR, used);
#if AUDIO_DIAG_LOG
    dbg_sai_tx_err_events++;
    dbg_sai_tx_last_err = error_code;
    dbg_sai_tx_sr_flags |= status_flags;
#endif
}

void audio_diagnostics_record_sai_rx_error(uint32_t error_code,
                                           uint32_t status_flags)
{
    g_audio_rx_diagnostics.sai_error_events++;
    g_audio_rx_diagnostics.last_sai_error_code   = error_code;
    g_audio_rx_diagnostics.last_sai_status_flags = status_flags;
#if AUDIO_DIAG_LOG
    dbg_sai_rx_err_events++;
    dbg_sai_rx_last_err = error_code;
    dbg_sai_rx_sr_flags |= status_flags;
#endif
}

void audio_diagnostics_record_recovery_request(uint32_t cause_mask,
                                               uint32_t dma_error_code,
                                               uint32_t sai_error_code,
                                               uint32_t sai_status_flags)
{
    g_audio_recovery_diagnostics.request_count++;
    g_audio_recovery_diagnostics.last_cause_mask               = cause_mask;
    g_audio_recovery_diagnostics.last_request_dma_error_code   = dma_error_code;
    g_audio_recovery_diagnostics.last_request_sai_error_code   = sai_error_code;
    g_audio_recovery_diagnostics.last_request_sai_status_flags = sai_status_flags;
    g_audio_recovery_diagnostics.last_request_tick_ms          = HAL_GetTick();
}

void audio_diagnostics_record_recovery_attempt(void)
{
    g_audio_recovery_diagnostics.attempt_count++;
    g_audio_recovery_diagnostics.last_attempt_tick_ms = HAL_GetTick();
}

void audio_diagnostics_record_recovery_success(void)
{
    g_audio_recovery_diagnostics.success_count++;
    g_audio_recovery_diagnostics.consecutive_failures = 0u;
    g_audio_recovery_diagnostics.last_success_tick_ms = HAL_GetTick();
}

void audio_diagnostics_record_recovery_failure(uint32_t failed_stage)
{
    g_audio_recovery_diagnostics.failure_count++;
    g_audio_recovery_diagnostics.consecutive_failures++;
    g_audio_recovery_diagnostics.last_failed_stage = failed_stage;
    g_audio_recovery_diagnostics.last_failure_tick_ms = HAL_GetTick();
}

void audio_diagnostics_set_recovery_latched(bool latched)
{
    g_audio_recovery_diagnostics.latched = latched ? 1u : 0u;
    if (!latched)
    {
        g_audio_recovery_diagnostics.consecutive_failures = 0u;
    }
}

void audio_diagnostics_update_rate_snapshot(uint32_t state,
                                            uint32_t applied_hz,
                                            uint32_t applied_valid,
                                            uint32_t clock_valid)
{
    const uint32_t primask = __get_PRIMASK();
    __disable_irq();

    g_audio_rate_switch_diagnostics.state         = state;
    g_audio_rate_switch_diagnostics.last_applied_hz = applied_hz;
    g_audio_rate_switch_diagnostics.applied_valid = applied_valid ? 1u : 0u;
    g_audio_rate_switch_diagnostics.clock_valid   = clock_valid ? 1u : 0u;

    __set_PRIMASK(primask);
}

void audio_diagnostics_record_rate_switch_attempt(uint32_t target_hz, uint32_t sequence)
{
    g_audio_rate_switch_diagnostics.attempt_count++;
    g_audio_rate_switch_diagnostics.last_target_hz = target_hz;
    g_audio_rate_switch_diagnostics.last_sequence  = sequence;
    g_audio_rate_switch_diagnostics.last_attempt_tick_ms = HAL_GetTick();
}

void audio_diagnostics_record_rate_switch_noop(uint32_t target_hz, uint32_t sequence)
{
    g_audio_rate_switch_diagnostics.noop_count++;
    g_audio_rate_switch_diagnostics.last_target_hz = target_hz;
    g_audio_rate_switch_diagnostics.last_sequence  = sequence;
}

void audio_diagnostics_record_rate_switch_success(uint32_t applied_hz)
{
    g_audio_rate_switch_diagnostics.success_count++;
    g_audio_rate_switch_diagnostics.last_applied_hz    = applied_hz;
    g_audio_rate_switch_diagnostics.last_success_tick_ms = HAL_GetTick();
}

void audio_diagnostics_record_rate_switch_failure(uint32_t failed_result,
                                                  uint32_t failed_stage,
                                                  uint32_t hal_status,
                                                  uint32_t aux_status)
{
    g_audio_rate_switch_diagnostics.failure_count++;
    g_audio_rate_switch_diagnostics.last_failed_result     = failed_result;
    g_audio_rate_switch_diagnostics.last_failed_stage      = failed_stage;
    g_audio_rate_switch_diagnostics.last_failed_hal_status = hal_status;
    g_audio_rate_switch_diagnostics.last_failed_aux_status = aux_status;
    g_audio_rate_switch_diagnostics.last_failure_tick_ms   = HAL_GetTick();
}

void audio_diagnostics_record_rate_switch_cleanup(uint32_t cleanup_status)
{
    g_audio_rate_switch_diagnostics.last_cleanup_status = cleanup_status;
}

#if AUDIO_DIAG_LOG
void audio_diagnostics_record_usb_out_packet(uint16_t bytes, uint32_t rx_cycle)
{
    dbg_usb_out_packet_events++;
    dbg_usb_out_packet_bytes += bytes;
    if (bytes < dbg_usb_out_packet_size_min)
    {
        dbg_usb_out_packet_size_min = bytes;
    }
    if (bytes > dbg_usb_out_packet_size_max)
    {
        dbg_usb_out_packet_size_max = bytes;
    }

    if (dbg_usb_out_prev_cycle_valid)
    {
        const uint32_t gap_cycles = rx_cycle - dbg_usb_out_prev_cycle;
        const uint32_t expected_cycles = SystemCoreClock / AUDIO_USB_HS_MICROFRAMES_PER_SECOND;
        const uint32_t late_threshold_cycles = expected_cycles + (expected_cycles / 2u);

        if (gap_cycles < dbg_usb_out_gap_cycles_min)
        {
            dbg_usb_out_gap_cycles_min = gap_cycles;
        }
        if (gap_cycles > dbg_usb_out_gap_cycles_max)
        {
            dbg_usb_out_gap_cycles_max = gap_cycles;
        }
        if (gap_cycles > late_threshold_cycles)
        {
            dbg_usb_out_gap_late_events++;
        }
    }
    dbg_usb_out_prev_cycle       = rx_cycle;
    dbg_usb_out_prev_cycle_valid = true;
}

void audio_diagnostics_record_usb_out_fifo(uint16_t fifo_count)
{
    if (fifo_count < dbg_usb_out_fifo_min)
    {
        dbg_usb_out_fifo_min = fifo_count;
    }
    if (fifo_count > dbg_usb_out_fifo_max)
    {
        dbg_usb_out_fifo_max = fifo_count;
    }
}

void audio_diagnostics_record_usb_out_feedback(uint32_t feedback)
{
    dbg_usb_out_fb_last = feedback;
    if (feedback < dbg_usb_out_fb_min)
    {
        dbg_usb_out_fb_min = feedback;
    }
    if (feedback > dbg_usb_out_fb_max)
    {
        dbg_usb_out_fb_max = feedback;
    }
}

void audio_diagnostics_record_usb_in_packet(uint16_t bytes)
{
    dbg_usb_in_packet_events++;
    dbg_usb_in_packet_bytes += bytes;
    if (bytes == 0u)
    {
        dbg_usb_in_packet_zero_events++;
    }
    if (bytes < dbg_usb_in_packet_size_min)
    {
        dbg_usb_in_packet_size_min = bytes;
    }
    if (bytes > dbg_usb_in_packet_size_max)
    {
        dbg_usb_in_packet_size_max = bytes;
    }
}

void audio_diagnostics_record_usb_in_write(uint16_t written, uint16_t requested)
{
    dbg_usb_in_write_bytes += written;
    if (written == 0U)
    {
        dbg_usb_in_write_zero_events++;
    }
    else if (written < requested)
    {
        dbg_usb_in_write_partial_events++;
    }
}

void audio_diagnostics_record_usb_in_fifo(uint16_t fifo_count)
{
    if (fifo_count < dbg_usb_in_fifo_min)
    {
        dbg_usb_in_fifo_min = fifo_count;
    }
    if (fifo_count > dbg_usb_in_fifo_max)
    {
        dbg_usb_in_fifo_max = fifo_count;
    }
}
#endif

#if AUDIO_DIAG_LOG || AUDIO_DIAG_DMA_TIME_REPORT
// deadline_cyclesの表示用換算。未計測(0)と期限なし(UINT32_MAX)は0で表示する。
static uint32_t audio_diagnostics_deadline_us(uint32_t deadline_cycles)
{
    if ((deadline_cycles == 0u) || (deadline_cycles == UINT32_MAX))
    {
        return 0u;
    }
    return audio_diagnostics_cycles_to_us(deadline_cycles);
}

// DMA処理完了時間の出力。計測値はAudio Task contextだけが更新する。
// 呼出側は出力前に値を確定したスナップショットを渡す。
static void audio_diagnostics_log_tx_dma_time(const audio_tx_diagnostics_t* tx)
{
    SEGGER_RTT_printf(0,
                      "[AUD][TX-DMA-TIME] proc_us half/cplt=%lu/%lu complete_us half/cplt=%lu/%lu complete_deadline_us half/cplt=%lu/%lu overruns half/cplt=%lu/%lu\r\n",
                      (unsigned long) audio_diagnostics_cycles_to_us(tx->half_process_cycles_max),
                      (unsigned long) audio_diagnostics_cycles_to_us(tx->cplt_process_cycles_max),
                      (unsigned long) audio_diagnostics_cycles_to_us(tx->half_complete_cycles_max),
                      (unsigned long) audio_diagnostics_cycles_to_us(tx->cplt_complete_cycles_max),
                      (unsigned long) audio_diagnostics_deadline_us(tx->half_complete_deadline_cycles_at_max),
                      (unsigned long) audio_diagnostics_deadline_us(tx->cplt_complete_deadline_cycles_at_max),
                      (unsigned long) tx->half_complete_deadline_overruns,
                      (unsigned long) tx->cplt_complete_deadline_overruns);
}

static void audio_diagnostics_log_rx_dma_time(const audio_rx_diagnostics_t* rx)
{
    SEGGER_RTT_printf(0,
                      "[AUD][RX-DMA-TIME] proc_us half/cplt=%lu/%lu complete_us half/cplt=%lu/%lu complete_deadline_us half/cplt=%lu/%lu overruns half/cplt=%lu/%lu\r\n",
                      (unsigned long) audio_diagnostics_cycles_to_us(rx->rx_half_process_cycles_max),
                      (unsigned long) audio_diagnostics_cycles_to_us(rx->rx_cplt_process_cycles_max),
                      (unsigned long) audio_diagnostics_cycles_to_us(rx->rx_half_complete_cycles_max),
                      (unsigned long) audio_diagnostics_cycles_to_us(rx->rx_cplt_complete_cycles_max),
                      (unsigned long) audio_diagnostics_deadline_us(rx->rx_half_complete_deadline_cycles_at_max),
                      (unsigned long) audio_diagnostics_deadline_us(rx->rx_cplt_complete_deadline_cycles_at_max),
                      (unsigned long) rx->rx_half_complete_deadline_overruns,
                      (unsigned long) rx->rx_cplt_complete_deadline_overruns);
}

// USB OUT FIFOの直接読出し（#260）の累計。TX診断と同じくOUT開始・レート変更以降の値。
static void audio_diagnostics_log_tx_out(const audio_tx_diagnostics_t* tx)
{
    SEGGER_RTT_printf(0,
                      "[AUD][TX-OUT] underrun=%lu drift_up/down=%lu/%lu stale=%lu full=%lu overflow=%lu discard=%lu lost_min=%lu unknown=%lu reprime=%lu take_max_us=%lu fifo_words_min/max=%lu/%lu\r\n",
                      (unsigned long) tx->underrun_events,
                      (unsigned long) tx->drift_up_events,
                      (unsigned long) tx->drift_down_events,
                      (unsigned long) tx->out_stale_request_skips,
                      (unsigned long) tx->out_fifo_full_events,
                      (unsigned long) tx->out_fifo_overflow_recoveries,
                      (unsigned long) tx->out_fifo_overflow_discard_bytes,
                      (unsigned long) tx->out_fifo_overflow_lost_bytes,
                      (unsigned long) tx->out_fifo_overflow_unknown_events,
                      (unsigned long) tx->out_reprime_events,
                      (unsigned long) audio_diagnostics_cycles_to_us(tx->out_take_section_cycles_max),
                      (unsigned long) ((tx->tx_used_min_words == UINT32_MAX) ? 0u : tx->tx_used_min_words),
                      (unsigned long) tx->tx_used_max_words);
}
#endif

#if AUDIO_DIAG_DMA_TIME_REPORT
// DMA half所有権確認（#251）の累計。TXはOUT開始・レート変更以降、RXは起動以降の値。
static void audio_diagnostics_log_dma_ownership(const audio_tx_diagnostics_t* tx,
                                                const audio_rx_diagnostics_t* rx)
{
    SEGGER_RTT_printf(0,
                      "[AUD][TX-DMA-OWN] skip=%lu boundary=%lu unknown=%lu q_max=%lu timeout=%lu stale=%lu fault=%lu suspend_max_us=%lu over_budget=%lu\r\n",
                      (unsigned long) tx->dma_commit_skips,
                      (unsigned long) tx->dma_commit_stream_boundary_events,
                      (unsigned long) tx->dma_commit_unknown_position_events,
                      (unsigned long) tx->dma_commit_entry_q_max,
                      (unsigned long) tx->dma_suspend_timeouts,
                      (unsigned long) tx->dma_suspend_stale_flag_clears,
                      (unsigned long) tx->dma_suspend_faults,
                      (unsigned long) audio_diagnostics_cycles_to_us(tx->dma_suspend_cycles_max),
                      (unsigned long) tx->dma_suspend_over_budget_events);
    SEGGER_RTT_printf(0,
                      "[AUD][RX-DMA-OWN] reject=%lu not_ready=%lu wait_max_us=%lu unknown=%lu q_max=%lu timeout=%lu stale=%lu fault=%lu suspend_max_us=%lu over_budget=%lu fifol_max=%lu fifol_over=%lu config_mismatch=%lu\r\n",
                      (unsigned long) rx->rx_dma_snapshot_rejects,
                      (unsigned long) rx->rx_dma_snapshot_not_ready_events,
                      (unsigned long) audio_diagnostics_cycles_to_us(rx->rx_dma_snapshot_wait_cycles_max),
                      (unsigned long) rx->rx_dma_snapshot_unknown_position_events,
                      (unsigned long) rx->rx_dma_snapshot_entry_q_max,
                      (unsigned long) rx->rx_dma_suspend_timeouts,
                      (unsigned long) rx->rx_dma_suspend_stale_flag_clears,
                      (unsigned long) rx->rx_dma_suspend_faults,
                      (unsigned long) audio_diagnostics_cycles_to_us(rx->rx_dma_suspend_cycles_max),
                      (unsigned long) rx->rx_dma_suspend_over_budget_events,
                      (unsigned long) rx->rx_dma_snapshot_fifol_max,
                      (unsigned long) rx->rx_dma_snapshot_fifol_over_capacity_events,
                      (unsigned long) rx->rx_dma_snapshot_config_mismatch_events);
}
#endif

void audio_diagnostics_report_dma_time(void)
{
#if AUDIO_DIAG_DMA_TIME_REPORT
    // 出力前に値を確定する。出力中に値は変わらない（更新するのは同じAudio Task）が、
    // 出力と同じ時点の値であることを明示するため、先にスナップショットを取る。
    const uint32_t primask = __get_PRIMASK();
    __disable_irq();
    const audio_tx_diagnostics_t tx = g_audio_tx_diagnostics;
    const audio_rx_diagnostics_t rx = g_audio_rx_diagnostics;
    __set_PRIMASK(primask);

    SEGGER_RTT_printf(0,
                      "[AUD][DMA-TIME-REPORT] tick=%lu\r\n",
                      (unsigned long) HAL_GetTick());
    audio_diagnostics_log_tx_dma_time(&tx);
    audio_diagnostics_log_rx_dma_time(&rx);
    audio_diagnostics_log_tx_out(&tx);
    audio_diagnostics_log_dma_ownership(&tx, &rx);
#endif
}

void audio_diagnostics_log_periodic(uint32_t sample_rate_hz,
                                    uint32_t task_frequency_hz,
                                    bool streaming_out,
                                    bool streaming_in,
                                    int32_t tx_used_words)
{
#if AUDIO_DIAG_LOG
    if (!streaming_out && !streaming_in)
    {
        return;
    }

    // USB OUT停止中（USB INのみ等）も、いずれかのstream動作中は
    // TX/RX両方向の完了時間を出力する。
    if (!streaming_out)
    {
        audio_diagnostics_log_tx_dma_time((const audio_tx_diagnostics_t*) &g_audio_tx_diagnostics);
        audio_diagnostics_log_rx_dma_time((const audio_rx_diagnostics_t*) &g_audio_rx_diagnostics);
        return;
    }

    uint32_t sigma_calls = sigma_spi_it_write_calls;
    uint32_t sigma_err   = sigma_spi_it_write_errors;
    uint32_t sigma_to    = sigma_spi_it_write_timeouts;
    uint32_t sigma_mto   = sigma_spi_it_mutex_timeouts;
    SEGGER_RTT_printf(0,
                      "[AUD][SUMMARY] sample_rate=%lu task_hz=%lu\r\n",
                      (unsigned long) sample_rate_hz,
                      (unsigned long) task_frequency_hz);
    SEGGER_RTT_printf(0,
                      "[AUD][TX-BUF] out_fifo_words=%ld min/max=%lu/%lu\r\n",
                      (long) tx_used_words,
                      (unsigned long) ((dbg_tx_used_min == DBG_MIN_U32_INIT) ? 0u : dbg_tx_used_min),
                      (unsigned long) dbg_tx_used_max);
    SEGGER_RTT_printf(0,
                      "[AUD][TX-EVENT] underrun=%lu partial=%lu drift_up/down=%lu/%lu\r\n",
                      (unsigned long) dbg_tx_underrun_events,
                      (unsigned long) dbg_tx_partial_fill_events,
                      (unsigned long) dbg_tx_drift_up_events,
                      (unsigned long) dbg_tx_drift_dn_events);
    SEGGER_RTT_printf(0,
                      "[AUD][TX-PRIME] wait=%lu complete=%lu drift_thr(up/down)=%lu/%lu drift_sup(up/down)=%lu/%lu\r\n",
                      (unsigned long) g_audio_tx_diagnostics.priming_wait_events,
                      (unsigned long) g_audio_tx_diagnostics.priming_completed_events,
                      (unsigned long) g_audio_tx_diagnostics.drift_up_threshold_events,
                      (unsigned long) g_audio_tx_diagnostics.drift_down_threshold_events,
                      (unsigned long) g_audio_tx_diagnostics.drift_up_suppressed_events,
                      (unsigned long) g_audio_tx_diagnostics.drift_down_suppressed_events);
    SEGGER_RTT_printf(0,
                      "[AUD][USB-OUT-FB] min/max/last=%lu/%lu/%lu\r\n",
                      (unsigned long) ((dbg_usb_out_fb_min == DBG_MIN_U32_INIT) ? 0u : dbg_usb_out_fb_min),
                      (unsigned long) dbg_usb_out_fb_max,
                      (unsigned long) dbg_usb_out_fb_last);
    audio_diagnostics_log_tx_out((const audio_tx_diagnostics_t*) &g_audio_tx_diagnostics);
    SEGGER_RTT_printf(0,
                      "[AUD][USB-IN-PKT] count=%lu zero=%lu bytes=%lu size_min/max=%u/%u\r\n",
                      (unsigned long) dbg_usb_in_packet_events,
                      (unsigned long) dbg_usb_in_packet_zero_events,
                      (unsigned long) dbg_usb_in_packet_bytes,
                      (unsigned int) ((dbg_usb_in_packet_size_min == DBG_MIN_U16_INIT) ? 0u : dbg_usb_in_packet_size_min),
                      (unsigned int) dbg_usb_in_packet_size_max);
    SEGGER_RTT_printf(0,
                      "[AUD][USB-IN-WR] zero=%lu partial=%lu\r\n",
                      (unsigned long) dbg_usb_in_write_zero_events,
                      (unsigned long) dbg_usb_in_write_partial_events);
    SEGGER_RTT_printf(0,
                      "[AUD][USB-IN-FIFO] bytes=%lu min/max=%u/%u\r\n",
                      (unsigned long) dbg_usb_in_write_bytes,
                      (unsigned int) ((dbg_usb_in_fifo_min == DBG_MIN_U16_INIT) ? 0u : dbg_usb_in_fifo_min),
                      (unsigned int) dbg_usb_in_fifo_max);
    SEGGER_RTT_printf(0,
                      "[AUD][REWRITE] tx_half/cplt=%lu/%lu rx_half/cplt=%lu/%lu\r\n",
                      (unsigned long) dbg_tx_half_rewrite_events,
                      (unsigned long) dbg_tx_cplt_rewrite_events,
                      (unsigned long) dbg_rx_half_rewrite_events,
                      (unsigned long) dbg_rx_cplt_rewrite_events);
    SEGGER_RTT_printf(0,
                      "[AUD][SAI] dma_err=%lu tx_err=%lu rx_err=%lu\r\n",
                      (unsigned long) dbg_dma_err_events,
                      (unsigned long) dbg_sai_tx_err_events,
                      (unsigned long) dbg_sai_rx_err_events);
    SEGGER_RTT_printf(0,
                      "[AUD][SAI-REG] tx_err=0x%08lX rx_err=0x%08lX tx_sr=0x%08lX rx_sr=0x%08lX\r\n",
                      (unsigned long) dbg_sai_tx_last_err,
                      (unsigned long) dbg_sai_rx_last_err,
                      (unsigned long) dbg_sai_tx_sr_flags,
                      (unsigned long) dbg_sai_rx_sr_flags);
    SEGGER_RTT_printf(0,
                      "[AUD][RX-DIAG] half/cplt=%lu/%lu rewrite=%lu/%lu drop_events=%lu dropped=%lu\r\n",
                      (unsigned long) g_audio_rx_diagnostics.rx_half_callbacks,
                      (unsigned long) g_audio_rx_diagnostics.rx_cplt_callbacks,
                      (unsigned long) g_audio_rx_diagnostics.rx_half_rewrite_events,
                      (unsigned long) g_audio_rx_diagnostics.rx_cplt_rewrite_events,
                      (unsigned long) g_audio_rx_diagnostics.rx_both_pending_events,
                      (unsigned long) g_audio_rx_diagnostics.rx_dma_events_dropped);
    SEGGER_RTT_printf(0,
                      "[AUD][DEADLINE] tx_half/cplt=%lu/%lu rx_half/cplt=%lu/%lu\r\n",
                      (unsigned long) g_audio_tx_diagnostics.half_deadline_overruns,
                      (unsigned long) g_audio_tx_diagnostics.cplt_deadline_overruns,
                      (unsigned long) g_audio_rx_diagnostics.rx_half_deadline_overruns,
                      (unsigned long) g_audio_rx_diagnostics.rx_cplt_deadline_overruns);
    SEGGER_RTT_printf(0,
                      "[AUD][USB-IN] start=%lu/%lu trim=%lu/%lu drop=%lu/%lu full=%lu stale=%lu zero/partial=%lu/%lu judged_max=%lu post_write_max=%lu section_max=%lu\r\n",
                      (unsigned long) g_audio_rx_diagnostics.usb_in_start_boundaries,
                      (unsigned long) g_audio_rx_diagnostics.usb_in_start_discard_words,
                      (unsigned long) g_audio_rx_diagnostics.usb_in_fifo_trim_events,
                      (unsigned long) g_audio_rx_diagnostics.usb_in_fifo_trim_bytes,
                      (unsigned long) g_audio_rx_diagnostics.usb_in_chunk_drop_events,
                      (unsigned long) g_audio_rx_diagnostics.usb_in_chunk_drop_bytes,
                      (unsigned long) g_audio_rx_diagnostics.usb_in_fifo_full_drops,
                      (unsigned long) g_audio_rx_diagnostics.usb_in_stale_request_skips,
                      (unsigned long) g_audio_rx_diagnostics.usb_in_write_zero_events,
                      (unsigned long) g_audio_rx_diagnostics.usb_in_write_partial_events,
                      (unsigned long) g_audio_rx_diagnostics.usb_in_fifo_judged_count_max,
                      (unsigned long) g_audio_rx_diagnostics.usb_in_fifo_post_write_max,
                      (unsigned long) g_audio_rx_diagnostics.usb_in_write_section_cycles_max);
    SEGGER_RTT_printf(0,
                      "[AUD][RECOVERY] req=%lu attempt=%lu ok=%lu fail=%lu consec=%lu latched=%lu cause=0x%02lX stage=%lu\r\n",
                      (unsigned long) g_audio_recovery_diagnostics.request_count,
                      (unsigned long) g_audio_recovery_diagnostics.attempt_count,
                      (unsigned long) g_audio_recovery_diagnostics.success_count,
                      (unsigned long) g_audio_recovery_diagnostics.failure_count,
                      (unsigned long) g_audio_recovery_diagnostics.consecutive_failures,
                      (unsigned long) g_audio_recovery_diagnostics.latched,
                      (unsigned long) g_audio_recovery_diagnostics.last_cause_mask,
                      (unsigned long) g_audio_recovery_diagnostics.last_failed_stage);
    SEGGER_RTT_printf(0,
                      "[AUD][RATE] state=%lu applied=%lu valid=%lu clk_valid=%lu target=%lu seq=%lu attempt/ok/fail/noop=%lu/%lu/%lu/%lu result=%lu stage=%lu hal=0x%08lX aux=0x%08lX cleanup=0x%02lX\r\n",
                      (unsigned long) g_audio_rate_switch_diagnostics.state,
                      (unsigned long) g_audio_rate_switch_diagnostics.last_applied_hz,
                      (unsigned long) g_audio_rate_switch_diagnostics.applied_valid,
                      (unsigned long) g_audio_rate_switch_diagnostics.clock_valid,
                      (unsigned long) g_audio_rate_switch_diagnostics.last_target_hz,
                      (unsigned long) g_audio_rate_switch_diagnostics.last_sequence,
                      (unsigned long) g_audio_rate_switch_diagnostics.attempt_count,
                      (unsigned long) g_audio_rate_switch_diagnostics.success_count,
                      (unsigned long) g_audio_rate_switch_diagnostics.failure_count,
                      (unsigned long) g_audio_rate_switch_diagnostics.noop_count,
                      (unsigned long) g_audio_rate_switch_diagnostics.last_failed_result,
                      (unsigned long) g_audio_rate_switch_diagnostics.last_failed_stage,
                      (unsigned long) g_audio_rate_switch_diagnostics.last_failed_hal_status,
                      (unsigned long) g_audio_rate_switch_diagnostics.last_failed_aux_status,
                      (unsigned long) g_audio_rate_switch_diagnostics.last_cleanup_status);
    SEGGER_RTT_printf(0,
                      "[AUD][SPI] calls=%lu errors=%lu timeouts=%lu mutex_timeouts=%lu\r\n",
                      (unsigned long) (sigma_calls - dbg_sigma_calls_prev),
                      (unsigned long) (sigma_err - dbg_sigma_err_prev),
                      (unsigned long) (sigma_to - dbg_sigma_to_prev),
                      (unsigned long) (sigma_mto - dbg_sigma_mto_prev));
    SEGGER_RTT_printf(0,
                      "[AUD][USB-OUT-PKT] packets=%lu bytes=%lu size_min/max=%u/%u\r\n",
                      (unsigned long) dbg_usb_out_packet_events,
                      (unsigned long) dbg_usb_out_packet_bytes,
                      (unsigned int) ((dbg_usb_out_packet_size_min == DBG_MIN_U16_INIT) ? 0u : dbg_usb_out_packet_size_min),
                      (unsigned int) dbg_usb_out_packet_size_max);
    SEGGER_RTT_printf(0,
                      "[AUD][USB-OUT-FIFO] min/max=%u/%u\r\n",
                      (unsigned int) ((dbg_usb_out_fifo_min == DBG_MIN_U16_INIT) ? 0u : dbg_usb_out_fifo_min),
                      (unsigned int) dbg_usb_out_fifo_max);
    SEGGER_RTT_printf(0,
                      "[AUD][USB-OUT-GAP] us_min/max=%lu/%lu late=%lu\r\n",
                      (unsigned long) ((dbg_usb_out_gap_cycles_min == DBG_MIN_U32_INIT) ? 0u : audio_diagnostics_cycles_to_us(dbg_usb_out_gap_cycles_min)),
                      (unsigned long) audio_diagnostics_cycles_to_us(dbg_usb_out_gap_cycles_max),
                      (unsigned long) dbg_usb_out_gap_late_events);
    dbg_sigma_calls_prev = sigma_calls;
    dbg_sigma_err_prev   = sigma_err;
    dbg_sigma_to_prev    = sigma_to;
    dbg_sigma_mto_prev   = sigma_mto;

    // 両方向の完了時間。いずれかのstream動作中に出力する。
    audio_diagnostics_log_tx_dma_time((const audio_tx_diagnostics_t*) &g_audio_tx_diagnostics);
    audio_diagnostics_log_rx_dma_time((const audio_rx_diagnostics_t*) &g_audio_rx_diagnostics);
#else
    (void) sample_rate_hz;
    (void) task_frequency_hz;
    (void) streaming_out;
    (void) streaming_in;
    (void) tx_used_words;
#endif
}

// ---- 診断のスナップショット（#251 改訂2） -----------------------------------------------

enum
{
    AUDIO_DIAGNOSTICS_SNAPSHOT_INTERVAL_MS = 100u,
};

_Static_assert((sizeof(audio_tx_diagnostics_t) % sizeof(uint32_t)) == 0u, "TX diagnostics must be word sized");
_Static_assert((sizeof(audio_rx_diagnostics_t) % sizeof(uint32_t)) == 0u, "RX diagnostics must be word sized");
_Static_assert((sizeof(audio_recovery_diagnostics_t) % sizeof(uint32_t)) == 0u, "recovery diagnostics must be word sized");
_Static_assert((sizeof(audio_window_totals_t) % sizeof(uint32_t)) == 0u, "window totals must be word sized");

static uint32_t s_snapshot_last_publish_ms;

// 32bit単位のvolatileコピー（非キャッシュ領域への書込みを1語ずつに保つ）。
static void audio_diagnostics_copy_words(volatile void* dst, const volatile void* src, size_t bytes)
{
    volatile uint32_t* d       = (volatile uint32_t*) dst;
    const volatile uint32_t* s = (const volatile uint32_t*) src;
    for (size_t i = 0; i < (bytes / sizeof(uint32_t)); i++)
    {
        d[i] = s[i];
    }
}

void audio_diagnostics_snapshot_reset(void)
{
    volatile uint32_t* words = (volatile uint32_t*) &g_audio_diagnostics_snapshot;
    for (size_t i = 0; i < (sizeof(g_audio_diagnostics_snapshot) / sizeof(uint32_t)); i++)
    {
        words[i] = 0u;
    }
    __DSB();
    s_snapshot_last_publish_ms = 0u;
}

void audio_diagnostics_publish_snapshot(uint32_t now_ms)
{
    volatile audio_diagnostics_snapshot_t* snap = &g_audio_diagnostics_snapshot;

    if ((snap->snapshot_count != 0u) && ((now_ms - s_snapshot_last_publish_ms) < AUDIO_DIAGNOSTICS_SNAPSHOT_INTERVAL_MS))
    {
        return;
    }
    s_snapshot_last_publish_ms = now_ms;

    // 写すのはAudio Taskだけ。ISRが元の診断を途中で更新しても、各語は32bit単位で読むので
    // 語の途中の値にはならない（構造体全体の同時性は求めない）。PRIMASKは使わない。
    const uint32_t odd  = snap->sequence + 1u;
    const uint32_t even = odd + 1u;

    snap->sequence_end = odd;
    __DMB();
    snap->sequence = odd;
    __DMB();

    snap->tick_ms        = now_ms;
    snap->snapshot_count = snap->snapshot_count + 1u;
    audio_diagnostics_copy_words(&snap->tx, &g_audio_tx_diagnostics, sizeof(snap->tx));
    audio_diagnostics_copy_words(&snap->rx, &g_audio_rx_diagnostics, sizeof(snap->rx));
    audio_diagnostics_copy_words(&snap->recovery, &g_audio_recovery_diagnostics, sizeof(snap->recovery));
    audio_diagnostics_copy_words(&snap->totals, &g_audio_window_totals, sizeof(snap->totals));
    __DMB();

    snap->sequence_end = even;
    __DMB();
    snap->sequence = even;
    __DSB();
}
