yamamo2shun1/JUMBLEQ/STM32CubeIDE/JUMBLEQ/Appli/Core/Src/audio_diagnostics_internal.h

/*
 * audio_diagnostics_internal.h
 *
 * Private recording API for the audio diagnostics counters. The functions are
 * called from USB/DMA ISR context (transport) and from the Audio Task; they
 * only update fixed-size counters, min/max values and timestamps.
 *
 * AUDIO_DIAG_LOG selects the RTT interval summary. AUDIO_DIAG_DMA_TIME_REPORT
 * (measurement builds only) prints the DMA timing once when both streams stop.
 * The defaults live here so every audio module sees the same value from the
 * build flags.
 */

#ifndef AUDIO_DIAGNOSTICS_INTERNAL_H_
#define AUDIO_DIAGNOSTICS_INTERNAL_H_

#include <stdbool.h>
#include <stddef.h>
#include <stdint.h>

#ifndef AUDIO_DIAG_LOG
#define AUDIO_DIAG_LOG 0
#endif

// 1の場合、OUT/INの両方が停止した遷移時に一度だけ、DMA処理時間とOUT診断をRTTへ
// 出力する。周期ログ（AUDIO_DIAG_LOG）を出さずに、CPUから読んだ値で測定するための
// 確認用ビルドで使う。
#ifndef AUDIO_DIAG_DMA_TIME_REPORT
#define AUDIO_DIAG_DMA_TIME_REPORT 0
#endif

// 1の場合、DMA half所有権確認（#251）の試験用遅延注入とトレースを有効にする。
// 試験ビルド専用で、製品ビルドでは0のまま（注入のコードと変数を生成しない）。
#ifndef AUDIO_DMA_OWNERSHIP_TEST
#define AUDIO_DMA_OWNERSHIP_TEST 0
#endif

// DMA half所有権確認（GPDMA一時停止中のcommit/snapshot）の結果。transportと共通の値。
enum
{
    AUDIO_DIAG_DMA_OWN_OK = 0u,           // 所有権を確認してアクセスした
    AUDIO_DIAG_DMA_OWN_BUSY,              // TX: DMAがhalfを読んでいる途中（skip）、RX: 書いている途中（reject）
    AUDIO_DIAG_DMA_OWN_NOT_READY,         // RXのみ: halfの末尾がDMA FIFOに残っている可能性がある
    AUDIO_DIAG_DMA_OWN_UNKNOWN,           // チャネル無効・エラー・不正なBNDT・停止後の状態不一致
    AUDIO_DIAG_DMA_OWN_SUSPEND_TIMEOUT,   // 期限内にSUSPFが立たなかった
    AUDIO_DIAG_DMA_OWN_SUSPEND_FAULT,     // 停止状態異常（ラッチ中、または解除を確かめられない）
    AUDIO_DIAG_DMA_OWN_STREAM_BOUNDARY,   // TXのみ: 未適用のstream要求があり、旧streamの音声を書かなかった
};

// USB OUT -> SAI TX経路の軽量診断。RTT出力は行わず、デバッガから参照する。
enum
{
    AUDIO_TX_DIAG_EVENT_BOTH_PENDING = (1u << 0),
    AUDIO_TX_DIAG_EVENT_HALF_REWRITE = (1u << 1),
    AUDIO_TX_DIAG_EVENT_CPLT_REWRITE = (1u << 2),
    AUDIO_TX_DIAG_EVENT_UNDERRUN     = (1u << 3),
    AUDIO_TX_DIAG_EVENT_PARTIAL_FILL = (1u << 4),
    AUDIO_TX_DIAG_EVENT_DRIFT_UP     = (1u << 5),
    AUDIO_TX_DIAG_EVENT_DRIFT_DOWN   = (1u << 6),
    AUDIO_TX_DIAG_EVENT_DMA_ERROR    = (1u << 7),
    AUDIO_TX_DIAG_EVENT_SAI_ERROR    = (1u << 8),
};

typedef struct
{
    uint32_t reset_count;
    uint32_t tx_half_callbacks;
    uint32_t tx_cplt_callbacks;
    uint32_t both_pending_events;
    uint32_t dma_events_dropped;
    uint32_t half_rewrite_events;
    uint32_t cplt_rewrite_events;
    uint32_t underrun_events;
    uint32_t partial_fill_events;
    uint32_t drift_up_events;
    uint32_t drift_down_events;
    uint32_t dma_error_events;
    uint32_t sai_error_events;
    // tx_used_*/last_event_used_words: USB OUT FIFO水位（word、half処理開始時＝読出し直前）。
    uint32_t tx_used_min_words;
    uint32_t tx_used_max_words;
    int32_t  last_event_used_words;
    uint32_t last_event_flags;
    uint32_t last_event_tick_ms;
    uint32_t last_event_cycle;
    uint32_t last_pending_callback;  // 1: half, 2: complete
    uint32_t both_pending_last_callback;
    uint32_t half_service_cycles_max;
    uint32_t cplt_service_cycles_max;
    uint32_t last_dma_error_code;
    uint32_t last_sai_error_code;
    uint32_t last_sai_status_flags;
    uint32_t half_deadline_overruns;
    uint32_t cplt_deadline_overruns;
    uint32_t priming_wait_events;         // priming待機で無音出力したhalf数
    uint32_t priming_completed_events;    // priming完了回数
    uint32_t drift_up_threshold_events;   // 上側開始閾値への逸脱回数（補正の有無に依らない）
    uint32_t drift_down_threshold_events; // 下側開始閾値への逸脱回数
    uint32_t drift_up_suppressed_events;  // 逸脱継続したが最小間隔制限で見送った回数
    uint32_t drift_down_suppressed_events;
    // DMA処理完了時間（DWT->CYCCNT基準、割り込み／Taskプリエンプト時間を含む）。
    // process=処理開始→完了、complete=callback→完了。deadline=DMA half期間
    // （half frame数/実サンプルレート）。complete最大値の更新時はその時点のdeadlineも
    // 同時に保存する。UINT32_MAXは期限なし（レート未確定）。
    uint32_t half_process_cycles_max;
    uint32_t cplt_process_cycles_max;
    uint32_t half_complete_cycles_max;
    uint32_t cplt_complete_cycles_max;
    uint32_t half_complete_deadline_cycles_at_max;
    uint32_t cplt_complete_deadline_cycles_at_max;
    uint32_t half_complete_deadline_overruns;
    uint32_t cplt_complete_deadline_overruns;
    uint32_t last_process_cycles;
    uint32_t last_complete_cycles;
    uint32_t last_complete_deadline_cycles;
    // USB OUT FIFOの直接読出し（#260）。
    uint32_t out_stale_request_skips;          // 未適用のstream要求があり読まなかったhalf数
    uint32_t out_fifo_full_events;             // packet書込み後にFIFOが満杯（上書きの可能性。USB ISRで検出）
    uint32_t out_fifo_overflow_recoveries;     // 満杯・overflowを検出してFIFOをclearした回数
    uint32_t out_fifo_overflow_discard_bytes;  // そのclearでアプリが破棄した有効データ(byte)の累計
    // raw count > depthで観測できた上書き量(byte)の累計。二重overflowで失われた量は
    // 観測できないため、上書きによる累積喪失量の下限として扱う。
    uint32_t out_fifo_overflow_lost_bytes;
    // raw count == depthの満杯でclearした回数（二重overflowの可能性があり喪失量不明）。
    // 二重overflow後にさらに書き込まれるとraw count > depthに戻るため、二重overflowの
    // 全件を数えるものではない。
    uint32_t out_fifo_overflow_unknown_events;
    uint32_t out_reprime_events;               // FIFOが空になりprimingへ戻した回数
    uint32_t out_take_section_cycles_max;      // FIFO読出しPRIMASK区間の最大サイクル数
    // DMA half所有権確認（#251）。作業バッファ→DMA halfのcommitをGPDMA一時停止中に行う。
    uint32_t dma_commit_skips;                   // DMAがhalfを読んでいる途中で書かなかった回数
    uint32_t dma_commit_stream_boundary_events;  // 旧streamの音声を無音へ置き換えた回数
    uint32_t dma_commit_unknown_position_events; // 状態・位置を確かめられず書かなかった回数
    uint32_t dma_commit_entry_q_max;             // committed時の停止位置q（相手halfの先頭から、word）の最大
    uint32_t dma_suspend_timeouts;               // 期限内にSUSPFが立たなかった回数
    uint32_t dma_suspend_stale_flag_clears;      // 開始前に古いSUSPFをクリアした回数
    uint32_t dma_suspend_faults;                 // 停止状態異常（以後アクセスせず復旧を要求）
    uint32_t dma_suspend_cycles_max;             // SUSP書込み→解除完了の最大サイクル数
    uint32_t dma_suspend_over_budget_events;     // 停止期間がframe周期の半分を超えた回数（性能目標の超過）
} audio_tx_diagnostics_t;

extern volatile audio_tx_diagnostics_t g_audio_tx_diagnostics;
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
